jrhun/TeensyEngine/buildLog/designProfile.PNG

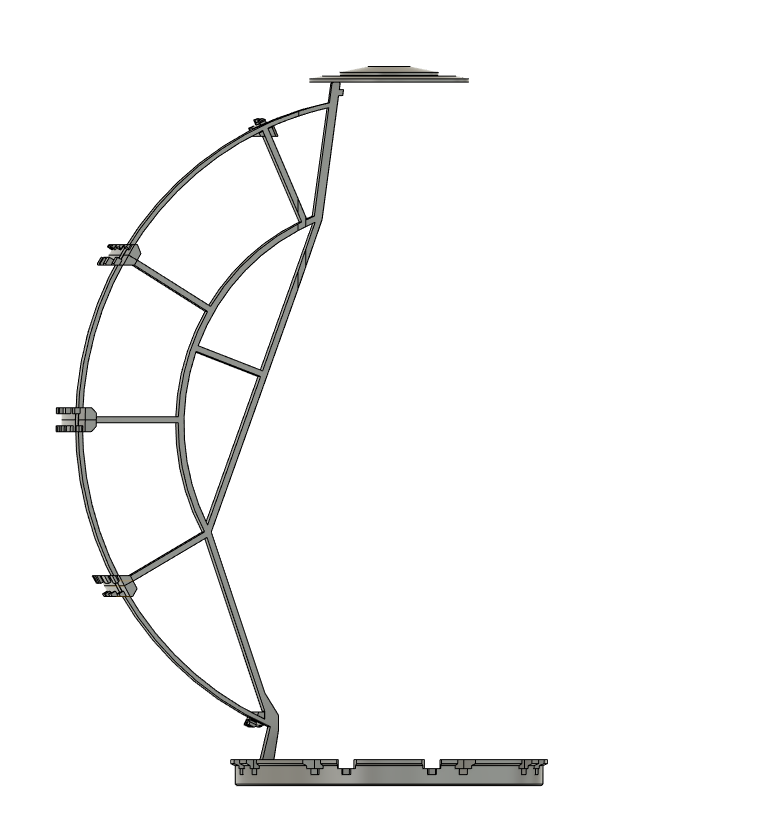
buildLog/designProfile.PNG
