jrhun/TeensyEngine/buildLog/PCB_design-front.PNG

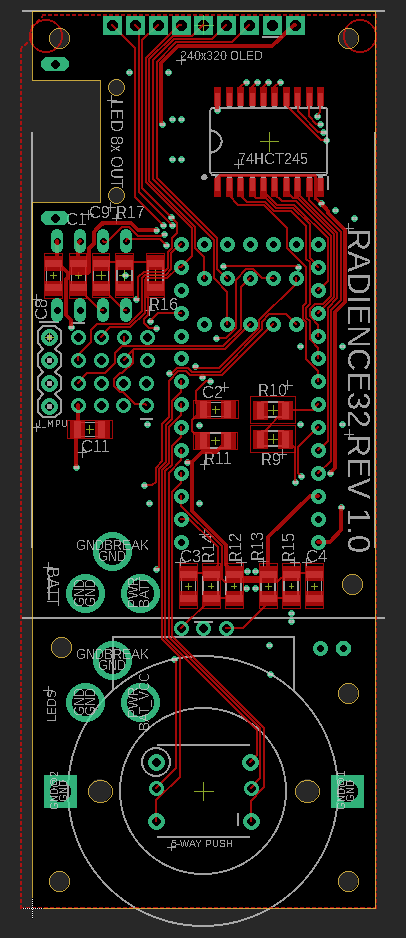
buildLog/PCB_design-front.PNG
