jrhun/TeensyEngine/images/flower/pixel_flowers_stages_of_blooming__16x16_px__by_brysiaa_de5okf2-fullview.jpg

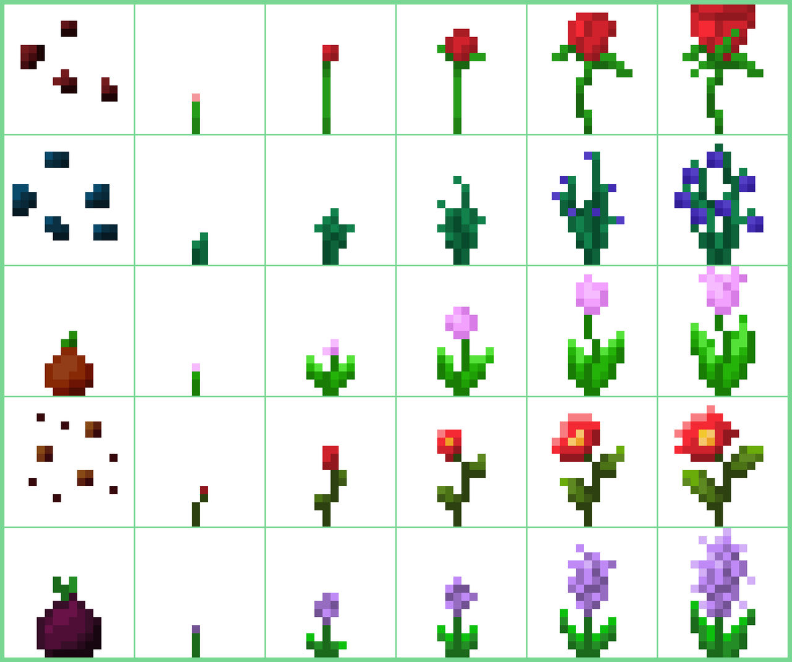
images/flower/pixel_flowers_stages_of_blooming__16x16_px__by_brysiaa_de5okf2-fullview.jpg
