jrhun/TeensyEngine/ledControl.h

//#ifndef LEDS_H
//#define LEDS_H
//
//#include "data.h"
//
////things to try stop flickering
////1
////#define FASTLED_ALLOW_INTERRUPTS
////2
//// change first pin to one earlier i.e 25 and skip first NUM_LEDS_PER_STRIP
//#include <FastLED.h>
////#include <FastLED_GFX.h>
////#include <Fonts/PicopixelFL.h>
//
//#define ROWS                32
//#define COLS                64
//#define NUM_LEDS            ROWS*COLS
//#define NUM_STRIPS          8
//#define NUM_LEDS_PER_STRIP  240  //we have 30 * 8 leds per strip
//#define LAST_VISIBLE_LED    1920  //(NUM_STRIPS * NUM_LEDS_PER_STRIP)
////#define FPS                 60
//
///*
//#if !defined(pgm_read_byte)
//#define pgm_read_byte(addr) (*(const unsigned char *)(addr))
//#endif
//#if !defined(pgm_read_word)
//#define pgm_read_word(addr) (*(const unsigned short *)(addr))
//#endif
//#if !defined(pgm_read_pointer)
//#define pgm_read_pointer(addr) ((void *)pgm_read_word(addr))
//#endif
//*/
//CRGBArray < NUM_LEDS > ledsRaw;
////uint8_t zBuffer[ROWS * COLS];
////CRGB scratchArray[NUM_LEDS]; // have global as ESP doesn't like variables on the stack
//CRGBPalette16 currentPalette;
//CRGBPalette16 targetPalette;
//TBlendType    currentBlending;
//uint8_t blendCounter = 0;
//bool blendActive = false;
//
//
////external variables
//
///*
//
//
//const uint8_t gGradientPaletteCount =
//  sizeof( gGradientPalettes) / sizeof( TProgmemRGBGradientPalettePtr );
//*/
//const uint8_t PROGMEM gamma8[] = {
//  0,   0,   0,   0,   0,   0,  0,  0,  0,  0,  0,  0,  0,  0,  0,  0,
//  0,   0,   0,   0,   0,   0,  0,  0,  0,  0,  0,  0,  1,  1,  1,  1,
//  1,   1,   1,   1,   1,   1,  1,  1,  1,  2,  2,  2,  2,  2,  2,  2,
//  2,   3,   3,   3,   3,   3,  3,  3,  4,  4,  4,  4,  4,  5,  5,  5,
//  5,   6,   6,   6,   6,   7,  7,  7,  7,  8,  8,  8,  9,  9,  9, 10,
//  10,  10,  11,  11,  11,  12, 12, 13, 13, 13, 14, 14, 15, 15, 16, 16,
//  17,  17,  18,  18,  19,  19, 20, 20, 21, 21, 22, 22, 23, 24, 24, 25,
//  25,  26,  27,  27,  28,  29, 29, 30, 31, 32, 32, 33, 34, 35, 35, 36,
//  37,  38,  39,  39,  40,  41, 42, 43, 44, 45, 46, 47, 48, 49, 50, 50,
//  51,  52,  54,  55,  56,  57, 58, 59, 60, 61, 62, 63, 64, 66, 67, 68,
//  69,  70,  72,  73,  74,  75, 77, 78, 79, 81, 82, 83, 85, 86, 87, 89,
//  90,  92,  93,  95,  96,  98, 99, 101, 102, 104, 105, 107, 109, 110, 112, 114,
//  115, 117, 119, 120, 122, 124, 126, 127, 129, 131, 133, 135, 137, 138, 140, 142,
//  144, 146, 148, 150, 152, 154, 156, 158, 160, 162, 164, 167, 169, 171, 173, 175,
//  177, 180, 182, 184, 186, 189, 191, 193, 196, 198, 200, 203, 205, 208, 210, 213,
//  215, 218, 220, 223, 225, 228, 231, 233, 236, 239, 241, 244, 247, 249, 252, 255
//};
//
//void adjustGamma(CRGB &colour) {
//  colour.r = gamma8[colour.r];
//  colour.g = gamma8[colour.g];
//  colour.b = gamma8[colour.b];
//
//  //method 2
//  //  colour.r = dim8_video(colour.r);
//  //  colour.g = dim8_video(colour.g);
//  //  colour.b = dim8_video(colour.b);
//}
//
//uint16_t XY(uint8_t x, uint8_t y) {
//  /*//leds are mapped serpentine with 2 offset with 30 leds in each row e.g.
//    0       60
//    1       61
//    2   59  62  119
//    3   ..  63  ..
//    ..  33  ..  93
//    29  32  89  92
//        31      91
//        30      90
//  */
//
//  if ( (x >= COLS) || (y >= ROWS) )
//    return LAST_VISIBLE_LED + 1;
//
//  uint16_t j;
//  uint16_t i = x * (ROWS - 2); // each column actually has 30 leds
//  if (x % 2 == 0) {// even row
//    if (y == 31  and x >= 16 and x < 48) {
//      return (LAST_VISIBLE_LED + (x * 2) + (y - 30));
//    }
//    if ((y == 30 or y == 31) and (x < 16 or x >= 48)) {
//      //      return LAST_VISIBLE_LED + 1;
//      return (LAST_VISIBLE_LED + (x * 2) + (y - 30));
//    }
//    if (x >= 16 and x < 48)
//      j = y - 1;
//    else j = y;
//  }
//  else {// if odd row flip the row
//    if (y == 0 or y == 1) {
//      //      return LAST_VISIBLE_LED + 1;
//      return (LAST_VISIBLE_LED + (x * 2) + y);
//    }
//    j = (ROWS - 1) - y; //
//
//  }
//  return (i + j);
//}
//
//
//class Leds {
//  public:
//    Leds() {};// : FastLED_GFX(COLS, ROWS) {}
//
//    void init() {
//      #if defined(ESP32)
//      FastLED.addLeds<WS2812B, 13, GRB>(ledsRaw, 0 * NUM_LEDS_PER_STRIP, NUM_LEDS_PER_STRIP).setCorrection( TypicalSMD5050 );
//      FastLED.addLeds<WS2812B, 12, GRB>(ledsRaw, 1 * NUM_LEDS_PER_STRIP, NUM_LEDS_PER_STRIP).setCorrection( TypicalSMD5050 );
//      FastLED.addLeds<WS2812B, 14, GRB>(ledsRaw, 2 * NUM_LEDS_PER_STRIP, NUM_LEDS_PER_STRIP).setCorrection( TypicalSMD5050 );
//      FastLED.addLeds<WS2812B, 27, GRB>(ledsRaw, 3 * NUM_LEDS_PER_STRIP, NUM_LEDS_PER_STRIP).setCorrection( TypicalSMD5050 );
//      FastLED.addLeds<WS2812B, 26, GRB>(ledsRaw, 4 * NUM_LEDS_PER_STRIP, NUM_LEDS_PER_STRIP).setCorrection( TypicalSMD5050 );
//      FastLED.addLeds<WS2812B, 25, GRB>(ledsRaw, 5 * NUM_LEDS_PER_STRIP, NUM_LEDS_PER_STRIP).setCorrection( TypicalSMD5050 );
//      FastLED.addLeds<WS2812B, 33, GRB>(ledsRaw, 6 * NUM_LEDS_PER_STRIP, NUM_LEDS_PER_STRIP).setCorrection( TypicalSMD5050 );
//      FastLED.addLeds<WS2812B, 32, GRB>(ledsRaw, 7 * NUM_LEDS_PER_STRIP, NUM_LEDS_PER_STRIP).setCorrection( TypicalSMD5050 );
//      // teensy 4.x
//      #elif defined(__IMXRT1052__) || defined(__IMXRT1062__) 
//      FastLED.addLeds<NUM_STRIPS, WS2812B, 19, GRB>(ledsRaw, NUM_LEDS_PER_STRIP).setCorrection( TypicalSMD5050 );
//      #endif 
//      
//      FastLED.setBrightness( *Data::brightness_t );
//	    
//
//      FastLED.setTemperature( DirectSunlight );
//      //      FastLED.setMaxPowerInVoltsAndMilliamps(5, 5000);
//
//      currentPalette = RainbowColors_p;
//      currentBlending = LINEARBLEND;
//
////      setFont(&Picopixel);
////      setTextSize(1);
////      setTextWrap(true);
//      FastLED.setDither( 0 );
//
//      #if 0
//      //test strips
//      uint8_t j = 0;
//      while(true){
////      setTextSize(2);
//      j += 5;
//      for (int i = 0; i < 8; i++) {
//        
////        ledsRaw(i*NUM_LEDS_PER_STRIP + 10, i*NUM_LEDS_PER_STRIP + 15).fill_solid(CHSV(i * 26, 255, 255));
//        ledsRaw(i*NUM_LEDS_PER_STRIP + 17, i*NUM_LEDS_PER_STRIP + 17 + i).fill_solid(CRGB::Red);
////        setTextColor(CHSV(j, 255, 255));
////        setCursor(1+ i * COLS / 8, 10);
////        print(i);
//      }
////      setTextSize(1);
//      FastLED.show();
//      delay(50);
//      }
//      delay(10000);
//      #endif
//    }
//
//    void show() {
//       FastLED.show();
//    }
//
//    void drawPixel(int16_t x, int16_t y, CRGB color) {
//      ledsRaw[XY(x, y)] = color;
//    }
//    void drawPixel(int16_t x, int16_t y, uint8_t hue) {
//      ledsRaw[XY(x, y)] = getColour(hue);
//    }
//
//    void drawPixel(int16_t x, int16_t y, CRGB color, uint8_t amount) {
//      if (ledsRaw[XY(x, y)])
//        ledsRaw[XY(x, y)] = blend(ledsRaw[XY(x, y)], color, amount);
//      else
//        ledsRaw[XY(x, y)] = color.nscale8(amount);
//    }
//
//    void setRow(uint8_t row, CRGB colour) {
//      for (uint8_t x = 0; x < COLS; x++) {
//        ledsRaw[XY(x, row)] = colour;
//      }
//    }
//
//    void setRowRainbow(uint8_t row, uint8_t hue) {
//      CRGB *rowReference[COLS];
//
//      for (uint8_t x = 0; x < COLS; x++) {
//        rowReference[x] = &ledsRaw[XY(x, row)];
//      }
//      fill_rainbow(rowReference[0], COLS, hue);
//    }
//
//    void setCol(uint8_t col, CRGB colour) {
//      for (uint8_t y = 0; y < ROWS; y++) {
//        ledsRaw[XY(col, y)] = colour;
//      }
//    }
//
//    void setColRainbow(uint8_t col, uint8_t hue) {
//      CRGB *colReference[ROWS];
//      for (uint8_t y = 0; y < ROWS; y++) {
//        colReference[y] = &ledsRaw[XY(col, y)];
//      }
//      fill_rainbow(colReference[0], ROWS, hue);
//    }
//
//    CRGB getColour(uint8_t offset = 0) {
//      CRGB colour = ColorFromPalette( currentPalette, Data::hue + offset);
//      if (Data::adjustGamma)
//        adjustGamma(colour);
//      return colour;
//    }
//
//    void drawBlend(uint8_t row, uint8_t col, CRGB colour, uint8_t blendAmount) {
//      if (ledsRaw[XY(row, col)]) // only blend if pixel is already lit
//        nblend(ledsRaw[XY(row, col)], colour, blendAmount);
//      else
//        drawPixel(row, col, colour);
//    }
//
//    void fade(uint8_t amount = Data::fadeAmount) {
//      ledsRaw.fadeToBlackBy(amount);
//    }
//
//    void clear() {
//      fillScreen(CRGB::Black);
//    }
//
//    void fillScreen(CRGB color) {
//      ledsRaw.fill_solid(color);
//    }
//
//    bool blendOnDrawPixel = false;
//
//    // GFX OVERRIDDEN CLASSES BELOW
////    void drawLine(int16_t x0, int16_t y0, int16_t x1, int16_t y1, CRGB color) {
////      int16_t steep = abs(y1 - y0) > abs(x1 - x0);
////      if (steep) {
////        adagfxswap(x0, y0);
////        adagfxswap(x1, y1);
////      }
////
////      if (x0 > x1) {
////        adagfxswap(x0, x1);
////        adagfxswap(y0, y1);
////      }
////
////      int16_t dx, dy;
////      dx = x1 - x0;
////      dy = abs(y1 - y0);
////
////      int16_t err = dx / 2;
////      int16_t ystep;
////
////      if (y0 < y1) {
////        ystep = 1;
////      } else {
////        ystep = -1;
////      }
////
////      for (; x0 <= x1; x0++) {
////        if (steep) {
////          drawPixel(y0 % COLS, x0, color);
////        } else {
////          drawPixel(x0 % COLS, y0, color);
////        }
////        err -= dy;
////        if (err < 0) {
////          y0 += ystep;
////          err += dx;
////        }
////      }
////    }
////
////    void drawRGBBitmap(int16_t x, int16_t y,
////                       const uint16_t bitmap[], int16_t w, int16_t h) {
////      for (int16_t j = 0; j < h; j++, y++) {
////        for (int16_t i = 0; i < w; i++ ) {
////          uint16_t color = pgm_read_word(&bitmap[j * w + i]);
////          drawPixel(x + i, y, CRGB( pgm_read_byte(&gamma5[ color >> 11       ]),
////                                    pgm_read_byte(&gamma6[(color >> 5) & 0x3F]),
////                                    pgm_read_byte(&gamma5[ color       & 0x1F])));
////        }
////      }
////    }
////
////    void drawRGBBitmap(int16_t x, int16_t y,
////                       const uint8_t bitmap[], int16_t w, int16_t h) {
////      uint16_t buffOffset = 0;
////      uint8_t r, g, b;
////      for (int16_t j = 0; j < h; j++, y++) {
////        for (int16_t i = 0; i < w; i++ ) {
////          r = pgm_read_word(&bitmap[buffOffset++]);
////          g = pgm_read_word(&bitmap[buffOffset++]);
////          b = pgm_read_word(&bitmap[buffOffset++]);
////          drawPixel(x + i, y, CRGB(r, g, b));
////        }
////      }
////    }
////
////    // draw gradient scale between two colours fg and bg
////    void drawGrayscaleBitmap(int16_t x, int16_t y,
////                             const uint8_t bitmap[], int16_t w, int16_t h, CRGB fg, CRGB bg) {
////      // col = x * cos( uint8_t((y - COLS/2)*6) );
////      //          uint16_t iOffset = ((x+i) * cos8( uint8_t(y-ROWS/2)*6 )) / 256;
////      // therefore, if x = 0, i = 10, y = 0iOffset =
////      // 10 * cos8(-96=160) / 256 = 6. a 4 unit reduction
////      // but then we also need to blend with the other 4 pixels... otherwise lastone takes preference
////      uint16_t buffidx = 0;
////      for (int16_t j = 0; j < h; j++) {
////        for (int16_t i = 0; i < w; i++ ) {
////          //          CRGB colour = blend(fg, bg, (uint8_t)pgm_read_byte(&bitmap[j * w + i]));
////          CRGB colour = blend(bg, fg, pgm_read_byte(bitmap + buffidx));
////          buffidx++;
////          drawPixel((x + i + COLS) % COLS, j + y, colour);
////        }
////      }
////    }
//
//};
//
//Leds ledControl;
//
//// PATTERNS
//
///*
//  // use a x y z array
//  // with a 4 sided cube (no top/bottom
//  // each side represents the 32x64 led matrix
//  // one side is 64/ 4 = 16 wide, and 32 tall
//  // coordinates would be
//  // if we have a 32*32*32 grid though that we generate once
//  // then move the cube through it and interpolate between values
//
//
//  split the matrix into 4 sections
//  16x32, 16x32, 16x32, 16x32
//  1st section FRONT
//  so we would take col = x 0 to 15, row = y = 0 to 31, z = 0
//
//  2nd section RIGHT
//  col = z = 0 to 15, row = y = 0 to 31, x = 15
//  3rd section BACK
//  col = x = 15 to 0, row = y = 0 to 31, z = 15
//  4th section LEFT
//  col = z = 15 to 0, row = y = 0 to 31, x = 0
//
//  then we also offset the whole thing by
//  xOffset = 0 to 16, then zOffset = 0 to 16, then xoffset 16 to 0, then zoffset 16 to 0
//
//
//*/
//
//
//
//
//
//
//#if defined (ESP32)
//// -- The core to run FastLED.show()
//#define FASTLED_SHOW_CORE 0
//
//// -- Task handles for use in the notifications
//static TaskHandle_t FastLEDshowTaskHandle = 0;
//static TaskHandle_t userTaskHandle = 0;
//
//void FastLEDshowESP32()
//{
//  if (userTaskHandle == 0) {
//    const TickType_t xMaxBlockTime = pdMS_TO_TICKS( 200 );
//    // -- Store the handle of the current task, so that the show task can
//    //    notify it when it's done
//    userTaskHandle = xTaskGetCurrentTaskHandle();
//
//    // -- Trigger the show task
//    xTaskNotifyGive(FastLEDshowTaskHandle);
//
//    // -- Wait to be notified that it's done
//    ulTaskNotifyTake(pdTRUE, xMaxBlockTime);
//    userTaskHandle = 0;
//  }
//}
//
//void FastLEDshowTask(void *pvParameters)
//{
//  const TickType_t xMaxBlockTime = pdMS_TO_TICKS( 500 );
//  // -- Run forever...
//  for (;;) {
//    // -- Wait for the trigger
//    ulTaskNotifyTake(pdTRUE, xMaxBlockTime);
//
//    // -- Do the show (synchronously)
//    FastLED.show();
//
//    // -- Notify the calling task
//    xTaskNotifyGive(userTaskHandle);
//  }
//}
//
//#endif //ESP32
//
//
//#endif //LEDS_H
