jrhun/TeensyEngine/motion.h

#include "MPU9250.h"
#include "data.h"

MPU9250 IMU(Wire2, 0x68);
int status;

//float aRes;
//float gRes;
float quat[4] = {1.0f, 0.0f, 0.0f, 0.0f};
float GyroMeasError = PI * (40.0f / 180.0f);   // gyroscope measurement error in rads/s (start at 40 deg/s)
float GyroMeasDrift = PI * (0.0f  / 180.0f);   // gyroscope measurement drift in rad/s/s (start at 0.0 deg/s/s)
// There is a tradeoff in the beta parameter between accuracy and response speed.
// In the original Madgwick study, beta of 0.041 (corresponding to GyroMeasError of 2.7 degrees/s) was found to give optimal accuracy.
// However, with this value, the LSM9SD0 response time is about 10 seconds to a stable initial quaternion.
// Subsequent changes also require a longish lag time to a stable output, not fast enough for a quadcopter or robot car!
// By increasing beta (GyroMeasError) by about a factor of fifteen, the response time constant is reduced to ~2 sec
// I haven't noticed any reduction in solution accuracy. This is essentially the I coefficient in a PID control sense; 
// the bigger the feedback coefficient, the faster the solution converges, usually at the expense of accuracy. 
// In any case, this is the free parameter in the Madgwick filtering and fusion scheme.
float beta = sqrt(3.0f / 4.0f) * GyroMeasError;   // compute beta
float zeta = sqrt(3.0f / 4.0f) * GyroMeasDrift; 

float deltat = 0.0f, sum = 0.0f;   
float pitch, roll;


void initMPU() {

  status = IMU.begin();
  if (status < 0) {
    Serial.println("IMU initialization unsuccessful");
    Serial.println("Check IMU wiring or try cycling power");
    Serial.print("Status: ");
    Serial.println(status);
  }

  // setting the accelerometer full scale range to +/-8G
  //  aRes = 8.0/32768.0;
  IMU.setAccelRange(MPU9250::ACCEL_RANGE_8G);
  // setting the gyroscope full scale range to +/-500 deg/s
  //  gRes = 500.0/32768.0;
  IMU.setGyroRange(MPU9250::GYRO_RANGE_500DPS);
  // setting DLPF bandwidth to 20 Hz
  IMU.setDlpfBandwidth(MPU9250::DLPF_BANDWIDTH_20HZ);
  // setting SRD to 19 for a 50 Hz update rate
  IMU.setSrd(19);

//  IMU.calibrateAccel();
//  if (status > 0)
//    Serial.println("Accel calibrated");

//  status = IMU.calibrateMag();
//  if (status > 0) {
//    Serial.println("Mag calibrated");
//  }
}


void updateMPU() {
  IMU.readSensor();
//  Data::ax = IMU.getAccelY_mss();
//  Data::ay = IMU.getAccelZ_mss();
//  Data::az = IMU.getAccelX_mss();
//  Data::gx = IMU.getGyroX_rads();
//  Data::gy = IMU.getGyroY_rads();
//  Data::gz = IMU.getGyroZ_rads();
}

void getPitchBasic(){
//  updateMPU();
  IMU.readSensor();
  
  const float alpha = 0.5;
  
  static double fXg = 0;
  static double fYg = 0;
  static double fZg = 0;
  //Low Pass Filter
    fXg = IMU.getAccelY_mss() * alpha + (fXg * (1.0 - alpha));
    fYg = IMU.getAccelZ_mss() * alpha + (fYg * (1.0 - alpha));
    fZg = IMU.getAccelX_mss() * alpha + (fZg * (1.0 - alpha));

    Data::ax = fXg; 
    Data::ay = fZg; 
    Data::az = fYg; //i dont understand why I had these different here and above, but it currently works and matches pitch/roll
 
    //Roll & Pitch Equations
    // initial pitch negative, roll positive
    // 1st try, pitch negative, roll negative
    Data::pitch  = -(atan2(-fYg, fZg)*180.0)/M_PI;
    Data::roll = -(atan2(fXg, sqrt(fYg*fYg + fZg*fZg))*180.0)/M_PI;

//  Serial.print("Pitch: ");
//  Serial.println(Data::pitch,5);
//  Serial.print("Roll: ");
//  Serial.println(Data::roll,5);
}


void MadgwickQuaternionUpdate(float ax, float ay, float az, float gx, float gy, float gz, float mx, float my, float mz)
{
  float q1 = quat[0], q2 = quat[1], q3 = quat[2], q4 = quat[3];   // short name local variable for readability
  float norm;
  float hx, hy, _2bx, _2bz;
  float s1, s2, s3, s4;
  float qDot1, qDot2, qDot3, qDot4;

  // Auxiliary variables to avoid repeated arithmetic
  float _2q1mx;
  float _2q1my;
  float _2q1mz;
  float _2q2mx;
  float _4bx;
  float _4bz;
  float _2q1 = 2.0f * q1;
  float _2q2 = 2.0f * q2;
  float _2q3 = 2.0f * q3;
  float _2q4 = 2.0f * q4;
  float _2q1q3 = 2.0f * q1 * q3;
  float _2q3q4 = 2.0f * q3 * q4;
  float q1q1 = q1 * q1;
  float q1q2 = q1 * q2;
  float q1q3 = q1 * q3;
  float q1q4 = q1 * q4;
  float q2q2 = q2 * q2;
  float q2q3 = q2 * q3;
  float q2q4 = q2 * q4;
  float q3q3 = q3 * q3;
  float q3q4 = q3 * q4;
  float q4q4 = q4 * q4;

  // Normalise accelerometer measurement
  norm = sqrtf(ax * ax + ay * ay + az * az);
  if (norm == 0.0f) return; // handle NaN
  norm = 1.0f / norm;
  ax *= norm;
  ay *= norm;
  az *= norm;

  // Normalise magnetometer measurement
  norm = sqrtf(mx * mx + my * my + mz * mz);
  if (norm == 0.0f) return; // handle NaN
  norm = 1.0f / norm;
  mx *= norm;
  my *= norm;
  mz *= norm;

  // Reference direction of Earth's magnetic field
  _2q1mx = 2.0f * q1 * mx;
  _2q1my = 2.0f * q1 * my;
  _2q1mz = 2.0f * q1 * mz;
  _2q2mx = 2.0f * q2 * mx;
  hx = mx * q1q1 - _2q1my * q4 + _2q1mz * q3 + mx * q2q2 + _2q2 * my * q3 + _2q2 * mz * q4 - mx * q3q3 - mx * q4q4;
  hy = _2q1mx * q4 + my * q1q1 - _2q1mz * q2 + _2q2mx * q3 - my * q2q2 + my * q3q3 + _2q3 * mz * q4 - my * q4q4;
  _2bx = sqrtf(hx * hx + hy * hy);
  _2bz = -_2q1mx * q3 + _2q1my * q2 + mz * q1q1 + _2q2mx * q4 - mz * q2q2 + _2q3 * my * q4 - mz * q3q3 + mz * q4q4;
  _4bx = 2.0f * _2bx;
  _4bz = 2.0f * _2bz;

  // Gradient decent algorithm corrective step
  s1 = -_2q3 * (2.0f * q2q4 - _2q1q3 - ax) + _2q2 * (2.0f * q1q2 + _2q3q4 - ay) - _2bz * q3 * (_2bx * (0.5f - q3q3 - q4q4) + _2bz * (q2q4 - q1q3) - mx) + (-_2bx * q4 + _2bz * q2) * (_2bx * (q2q3 - q1q4) + _2bz * (q1q2 + q3q4) - my) + _2bx * q3 * (_2bx * (q1q3 + q2q4) + _2bz * (0.5f - q2q2 - q3q3) - mz);
  s2 = _2q4 * (2.0f * q2q4 - _2q1q3 - ax) + _2q1 * (2.0f * q1q2 + _2q3q4 - ay) - 4.0f * q2 * (1.0f - 2.0f * q2q2 - 2.0f * q3q3 - az) + _2bz * q4 * (_2bx * (0.5f - q3q3 - q4q4) + _2bz * (q2q4 - q1q3) - mx) + (_2bx * q3 + _2bz * q1) * (_2bx * (q2q3 - q1q4) + _2bz * (q1q2 + q3q4) - my) + (_2bx * q4 - _4bz * q2) * (_2bx * (q1q3 + q2q4) + _2bz * (0.5f - q2q2 - q3q3) - mz);
  s3 = -_2q1 * (2.0f * q2q4 - _2q1q3 - ax) + _2q4 * (2.0f * q1q2 + _2q3q4 - ay) - 4.0f * q3 * (1.0f - 2.0f * q2q2 - 2.0f * q3q3 - az) + (-_4bx * q3 - _2bz * q1) * (_2bx * (0.5f - q3q3 - q4q4) + _2bz * (q2q4 - q1q3) - mx) + (_2bx * q2 + _2bz * q4) * (_2bx * (q2q3 - q1q4) + _2bz * (q1q2 + q3q4) - my) + (_2bx * q1 - _4bz * q3) * (_2bx * (q1q3 + q2q4) + _2bz * (0.5f - q2q2 - q3q3) - mz);
  s4 = _2q2 * (2.0f * q2q4 - _2q1q3 - ax) + _2q3 * (2.0f * q1q2 + _2q3q4 - ay) + (-_4bx * q4 + _2bz * q2) * (_2bx * (0.5f - q3q3 - q4q4) + _2bz * (q2q4 - q1q3) - mx) + (-_2bx * q1 + _2bz * q3) * (_2bx * (q2q3 - q1q4) + _2bz * (q1q2 + q3q4) - my) + _2bx * q2 * (_2bx * (q1q3 + q2q4) + _2bz * (0.5f - q2q2 - q3q3) - mz);
  norm = sqrtf(s1 * s1 + s2 * s2 + s3 * s3 + s4 * s4);    // normalise step magnitude
  norm = 1.0f / norm;
  s1 *= norm;
  s2 *= norm;
  s3 *= norm;
  s4 *= norm;

  // Compute rate of change of quaternion
  qDot1 = 0.5f * (-q2 * gx - q3 * gy - q4 * gz) - beta * s1;
  qDot2 = 0.5f * (q1 * gx + q3 * gz - q4 * gy) - beta * s2;
  qDot3 = 0.5f * (q1 * gy - q2 * gz + q4 * gx) - beta * s3;
  qDot4 = 0.5f * (q1 * gz + q2 * gy - q3 * gx) - beta * s4;

  // Integrate to yield quaternion
  q1 += qDot1 * deltat;
  q2 += qDot2 * deltat;
  q3 += qDot3 * deltat;
  q4 += qDot4 * deltat;
  norm = sqrtf(q1 * q1 + q2 * q2 + q3 * q3 + q4 * q4);    // normalise quaternion
  norm = 1.0f / norm;
  quat[0] = q1 * norm;
  quat[1] = q2 * norm;
  quat[2] = q3 * norm;
  quat[3] = q4 * norm;

}


void getPitch() {
  IMU.readSensor();
  MadgwickQuaternionUpdate(IMU.getAccelX_mss(), IMU.getAccelY_mss(), IMU.getAccelZ_mss(), IMU.getGyroX_rads(), IMU.getGyroY_rads(), IMU.getGyroZ_rads(),  IMU.getMagY_uT(),  IMU.getMagX_uT(), IMU.getMagZ_uT());
  pitch = -asin(2.0f * (quat[1] * quat[3] - quat[0] * quat[2]));
  pitch *= 180.0f / PI;
  roll  = atan2(2.0f * (quat[0] * quat[1] + quat[2] * quat[3]), quat[0] * quat[0] - quat[1] * quat[1] - quat[2] * quat[2] + quat[3] * quat[3]);
  roll *= 180.0f / PI;

  Serial.print("Pitch: ");
  Serial.println(pitch,5);
  Serial.print("Roll: ");
  Serial.println(roll,5);
}

void loopMPU() {
  IMU.readSensor();

  // display the data
  Serial.print(IMU.getAccelX_mss(), 6);
  Serial.print("\t");
  Serial.print(IMU.getAccelY_mss(), 6);
  Serial.print("\t");
  Serial.print(IMU.getAccelZ_mss(), 6);
  Serial.print("\t");
  Serial.print(IMU.getGyroX_rads(), 6);
  Serial.print("\t");
  Serial.print(IMU.getGyroY_rads(), 6);
  Serial.print("\t");
  Serial.print(IMU.getGyroZ_rads(), 6);
  Serial.print("\t");
  Serial.print(IMU.getMagX_uT(), 6);
  Serial.print("\t");
  Serial.print(IMU.getMagY_uT(), 6);
  Serial.print("\t");
  Serial.print(IMU.getMagZ_uT(), 6);
  Serial.print("\t");
  Serial.println(IMU.getTemperature_C(), 6);
}
