jrhun/TeensyEngine/src/Patterns/PatternPictures.h

#pragma once

#include "Pattern.h"

static const uint8_t PROGMEM world_64_32_8bit[2048] = {
	0x00, 0x00, 0x00, 0x00, 0x00, 0x00, 0x00, 0x00, 0x00, 0x00, 0x00, 0x00, 0x00, 0x00, 0x00, 0x00, 0x7f, 0xaa, 0xca, 0xb3, 0xaa, 0xaa, 0xbf, 0xcb, 0xcb, 0xb1, 0x4f, 0x00, 0x00, 0x00, 0x00, 0x00, 0x00, 0x00, 0x00, 0x00, 0x00, 0x00, 0x00, 0x00, 0x00, 0x00, 0x00, 0x00, 0x00, 0x00, 0x00, 0x00, 0x00, 0x00, 0x00, 0x00, 0x00, 0x00, 0x00, 0x00, 0x00, 0x00, 0x00, 0x00, 0x00, 0x00, 0x00, 0x00,
	0x00, 0x00, 0x00, 0x00, 0x00, 0x00, 0x00, 0x00, 0x00, 0x00, 0x4f, 0x8f, 0x90, 0x99, 0xb4, 0xb8, 0xd3, 0xa2, 0x8c, 0xd1, 0xff, 0xff, 0xff, 0xff, 0xff, 0x86, 0x00, 0x00, 0x00, 0x00, 0x00, 0x00, 0x00, 0x00, 0x00, 0x00, 0x00, 0x00, 0x00, 0x38, 0xb1, 0xd7, 0xcb, 0x70, 0x00, 0x00, 0x00, 0x00, 0x00, 0x00, 0x00, 0x00, 0x00, 0x00, 0x00, 0x00, 0x00, 0x00, 0x00, 0x00, 0x00, 0x00, 0x00, 0x00,
	0x00, 0x00, 0x00, 0x86, 0xb4, 0xbf, 0xaa, 0x7c, 0x9a, 0x91, 0xdd, 0xf6, 0xd9, 0xb8, 0xbc, 0xf2, 0xef, 0xb8, 0x00, 0x38, 0xfb, 0xff, 0xff, 0xff, 0xad, 0x00, 0x00, 0x00, 0x00, 0x00, 0x90, 0xc2, 0x91, 0x42, 0x00, 0x38, 0x80, 0xc0, 0xda, 0xfb, 0xff, 0xff, 0xff, 0xff, 0xff, 0xff, 0xdd, 0xd7, 0xe7, 0xd1, 0xc5, 0x90, 0x86, 0x90, 0x70, 0x00, 0x00, 0x00, 0x00, 0x00, 0x00, 0x00, 0x00, 0x00,
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
	0x0000, 0x8000, 0xdbe2, 0xdbe2, 0xdbe2, 0xdbe2, 0xdbe2, 0xdbe2, 0xdbe2, 0xdbe2, 0xdbe2, 0xdbe2, 0xdbe2, 0xdbe2, 0xdbe2, 0xdbe2, 0xdbe2, 0xdbe2, 0xdbe2, 0xdbe2, 0xdbe2, 0xdbe2, 0xdbe2, 0xdbe2, 0xdbe2, 0x8000, 0x0000
};

static const uint16_t PROGMEM mario_cloud_13_9_16bit[117] = {
	0x0000, 0x0000, 0x0000, 0x0000, 0x0000, 0x8000, 0x8000, 0x8000, 0x8000, 0x0000, 0x0000, 0x0000, 0x0000,
	0x0000, 0x0000, 0x0000, 0x0000, 0x8000, 0xffff, 0xffff, 0xffff, 0xffff, 0x8000, 0x0000, 0x0000, 0x0000,
	0x0000, 0x0000, 0x8000, 0x8000, 0xffff, 0xffff, 0xffff, 0xffff, 0xffff, 0xffff, 0x8000, 0x0000, 0x0000,
	0x0000, 0x8000, 0xffff, 0xffff, 0xffff, 0xffff, 0xffff, 0xffff, 0xffff, 0xffff, 0x8000, 0x0000, 0x0000,
	0x0000, 0x8000, 0xffff, 0x9eff, 0xffff, 0xffff, 0xffff, 0xffff, 0x9eff, 0xffff, 0xffff, 0x8000, 0x0000,
	0x8000, 0xffff, 0xffff, 0xffff, 0x9eff, 0x9eff, 0x9eff, 0x9eff, 0xffff, 0xffff, 0xffff, 0xffff, 0x8000,
	0x0000, 0x8000, 0xffff, 0xffff, 0xffff, 0xffff, 0xffff, 0xffff, 0xffff, 0xffff, 0xffff, 0xffff, 0x8000,
	0x0000, 0x0000, 0x8000, 0xffff, 0xffff, 0x8000, 0x8000, 0x8000, 0xffff, 0x8000, 0xffff, 0x8000, 0x0000,
	0x0000, 0x0000, 0x0000, 0x8000, 0x8000, 0x0000, 0x0000, 0x0000, 0x8000, 0x0000, 0x8000, 0x0000, 0x0000
};




#if !defined(pgm_read_byte)
#define pgm_read_byte(addr) (*(const unsigned char *)(addr))
#endif
#if !defined(pgm_read_word)
#define pgm_read_word(addr) (*(const unsigned short *)(addr))
#endif

#if !defined(pgm_read_qword)
#define pgm_read_qword(addr) (*(const unsigned long *)(addr))
#endif



// grayscale 8 bit image
void drawGrayscaleBitmap(int16_t x, int16_t y,
	const uint8_t bitmap[], int16_t w, int16_t h, CRGB fg, CRGB bg) {
	uint16_t buffidx = 0;
	for (int16_t j = 0; j < h; j++) {
		for (int16_t i = 0; i < w; i++) {
			//          CRGB colour = blend(fg, bg, (uint8_t)pgm_read_byte(&bitmap[j * w + i]));
			CRGB colour = blend(bg, fg, pgm_read_byte(bitmap + buffidx));
			buffidx++;
			gfx.putPixel((x + i + SCREEN_WIDTH) % SCREEN_WIDTH, j + y, colour);
		}
	}
}

void drawGrayscaleBitmapColour(int16_t x, int16_t y, const uint8_t bitmap[], int16_t w, int16_t h, uint8_t hue) {
	//colourise greyscale bitmap 0
	for (int16_t j = 0; j < h; j++) {
		for (int16_t i = 0; i < w; i++) {
			uint8_t color = pgm_read_byte(&bitmap[j * w + i]);
			if (color != 0x00) { //treat black as alpha 
				// if closer to white then turn down saturation 
				// clamp val at 128 minimum to keep from getting too dark 
				// 0 - 127
				uint8_t sat = 0;
				uint8_t val = 0;
				//if (color > 127) {
				//	// 128 - 255, val = 255, sat from 255 to 127
				//	val = 255; 
				//	sat = myMap(color, 128, 255, 255, 127);
				//}
				//else {
				//	sat = 255;
				//	val = color + 127;
				//}
				CRGB c = CHSV(hue, 255, color);
				gfx.putPixel((i + x) % SCREEN_WIDTH, j + y, c);
			}
		}
	}
}

// 16bit 565 encoded image
void drawRGBBitmap(int16_t x, int16_t y,
	const uint16_t bitmap[], int16_t w, int16_t h, float hueShift = 0.0) {
	if (hueShift != 0) {
		gfx.rotateCalculate(hueShift);
	}
	for (int16_t j = 0; j < h; j++) {
		for (int16_t i = 0; i < w; i++) {
			uint16_t color = pgm_read_word(&bitmap[j * w + i]);
			if (color != 0x0000) {
				//treat black as alpha
				if (hueShift == 0) {
					gfx.putPixel((x + i) % SCREEN_WIDTH, j + y, CRGB(pgm_read_byte(&gamma5[color >> 11]),
						pgm_read_byte(&gamma6[(color >> 5) & 0x3F]),
						pgm_read_byte(&gamma5[color & 0x1F])));
				}
				else {
					CRGB c = CRGB(pgm_read_byte(&gamma5[color >> 11]),
						pgm_read_byte(&gamma6[(color >> 5) & 0x3F]),
						pgm_read_byte(&gamma5[color & 0x1F]));
					gfx.putPixel((x + i) % SCREEN_WIDTH, j + y, gfx.rotate(c));
				}
			}
		}
	}
}

//16bit a555 encoded image
void drawARGBBitmap(int16_t x, int16_t y,
	const uint16_t bitmap[], int16_t w, int16_t h, bool flip = false) {

	for (int16_t j = 0; j < h; j++) {
		for (int16_t i = 0; i < w; i++) {
			uint16_t color = pgm_read_word(&bitmap[j * w + i]);
			if (((color >> 15) & 0x01) == 1) { //if alpha 
				uint8_t r = pgm_read_byte(&gamma5[(color >> 10) & 0x1F]);
				uint8_t g = pgm_read_byte(&gamma5[(color >> 5) & 0x1F]);
				uint8_t b = pgm_read_byte(&gamma5[(color >> 0) & 0x1F]);
				uint16_t xPos = (flip) ? SCREEN_WIDTH - i - 1 : i;
				gfx.putPixel((xPos + x) % SCREEN_WIDTH, j + y, CRGB(r, g, b));
			}
		}
	}
}



//24bit R8G8B8 encoded image
void drawRGBBitmap24bit(int16_t x, int16_t y,
	const uint8_t buf_u8[], int16_t w, int16_t h, float hueShift = 0.0) {
	uint8_t px_size = 3;
	if (hueShift != 0) {
		gfx.rotateCalculate(hueShift);
	}
	CRGB color;
	for (int16_t j = 0; j < h; j++) {
		for (int16_t i = 0; i < w; i++) {
			uint32_t px = w * j * px_size + i * px_size;
			color.r = buf_u8[px];
			color.g = buf_u8[px + 1];
			color.b = buf_u8[px + 2];
			if (hueShift != 0) {
				color = gfx.rotate(color);
			}
			gfx.putPixel((i + x) % SCREEN_WIDTH, j + y, color);
		}
	}


}

class PatternWorld : public _Pattern {
public:
	PatternWorld() : _Pattern("World") {}



	uint8_t drawFrame() {

		CRGB bg = CHSV(157, 255, 255);
		CRGB fg = CHSV(93, 255, 255);
		static uint16_t offset = SCREEN_WIDTH;
		static uint8_t offsetDelay = 0;
		//#if defined(ARDUINO)
		//		ledControl.drawGrayscaleBitmap(offset / 8, 0, world_64_32_8bit, 64, 32, fg, bg);
		//#else 
		//		
		uint16_t buffidx = 0;
		for (int16_t j = 0; j < SCREEN_HEIGHT; j++) {
			for (int16_t i = 0; i < SCREEN_WIDTH; i++) {
				CRGB colour = blend(bg, fg, (world_64_32_8bit[buffidx]));
				buffidx++;
				gfx.putPixel(((offset)+i + SCREEN_WIDTH) % SCREEN_WIDTH, j + 0, colour);
			}
		}
		//#endif
		offsetDelay = (offsetDelay + 1) % 6;
		if (offsetDelay == 0)
			offset--;
		if (offset < 0)
			offset = SCREEN_WIDTH;
		return returnVal;
	}


};

class PatternWorld2 : public _Pattern {
public:
	PatternWorld2() : _Pattern("World (no water)") {}



	uint8_t drawFrame() {

		CRGB bg = CHSV(0, 0, 0);
		CRGB fg = gfx.getColour();// CHSV(93, 255, 255);
		static uint16_t offset = SCREEN_WIDTH;
		static uint8_t offsetDelay = 0;
		//#if defined(ARDUINO)
		//		ledControl.drawGrayscaleBitmap(offset / 8, 0, world_64_32_8bit, 64, 32, fg, bg);
		//#else 
		//		
		uint16_t buffidx = 0;
		for (int16_t j = 0; j < SCREEN_HEIGHT; j++) {
			for (int16_t i = 0; i < SCREEN_WIDTH; i++) {
				fg = gfx.getColour(-i - j / 2);
				CRGB colour = blend(bg, fg, (world_64_32_8bit[buffidx]));
				buffidx++;
				gfx.putPixel(((offset)+i) % SCREEN_WIDTH, j + 0, colour);
			}
		}
		//#endif
		offsetDelay = (offsetDelay + 1) % 6;
		if (offsetDelay == 0)
			offset--;
		if (offset < 0)
			offset = SCREEN_WIDTH;

		return returnVal;
	}


};

class PatternMario : public _Pattern {
public:
	PatternMario() : _Pattern("Mario") {}

	uint8_t drawFrame() {
		_Pattern::drawFrame();

		frameCounter = (frameCounter + 1) % 12;
		if (frameCounter == 0) {
			marioPosX = (marioPosX + 1) % SCREEN_WIDTH;
		}
		//draw from back to front
		gfx.clear();
		gfx.fill(CRGB(90, 142, 245)); //mario background colour
		//ground
		for (uint8_t i = 0; i < 8; i++) {
			drawARGBBitmap(SCREEN_WIDTH + i * 8 - staticPos, groundPosY, mario_ground_8_8_16bit, 8, 8);
		}
		//bush
		drawARGBBitmap(SCREEN_WIDTH + 7 - staticPos, 14, mario_bush_27_10_16bit, 27, 10);

		//cloud
		drawARGBBitmap(cloudPosX, (frame < 2) ? 2 : 3, mario_cloud_13_9_16bit, 13, 9);



		//mario
		if (lastFrameUpdate + ((unsigned long)(frameUpdateDelay)) < GET_MILLIS()) {
			frame = (frame + 1) % 6; // 0 - 2
			lastFrameUpdate = GET_MILLIS();
			//if (frame % 3 == 0) {
			//marioPosX = (marioPosX + 1) % SCREEN_WIDTH;
			//}
			cloudPosX = (SCREEN_WIDTH + cloudPosX - 1) % SCREEN_WIDTH;
			if (frame % 2 == 0)
				staticPos = (staticPos + 1) % SCREEN_WIDTH;
		}
		if (jump) {
			jump--;
			// jump counts down from 128
			float v = 1.0 - float(jump) / float(jumpTime); // convert from 0 - 1
			float yPos = 0;

			if (v < 0.4) {
				yPos = myMap(v, 0.0, 0.4, 0, jumpHeight);
			}
			else if (v < 0.6) {
				yPos = jumpHeight;
			}
			else {
				yPos = myMap(v, 0.6, 1.0, jumpHeight, 0);
			}
			drawARGBBitmap(marioPosX, marioPosY - yPos, mario_jump_16_16_16bit, 16, 16);
		}
		else {
			if ((frame % 3) == 0) {
				drawARGBBitmap(marioPosX, marioPosY, mario1_16_16_16bit, 16, 16);
			}
			else if ((frame % 3) == 1) {
				drawARGBBitmap(marioPosX, marioPosY, mario2_16_16_16bit, 16, 16);
			}
			else if ((frame % 3) == 2) {
				drawARGBBitmap(marioPosX, marioPosY, mario3_16_16_16bit, 16, 16);

			}
		}

		return returnVal;
	}

	void trigger() {
		jump = jumpTime;
	}

	uint8_t frame = 0;
	uint8_t frameUpdateDelay = 100; //msec, 66msec = 15FPS
	uint8_t frameCounter = 0;
	uint8_t jump = 0;
	uint8_t jumpTime = 100;
	const uint8_t jumpHeight = 7;
	unsigned long lastFrameUpdate = 0;
	uint8_t marioPosX = 33; //positions are from the top down 
	uint8_t marioPosY = 9;
	uint8_t cloudPosX = 42;
	const uint8_t groundPosY = 24;
	uint8_t staticPos = 0;


};



static const uint16_t PROGMEM mushroom_12_11_16bit[132] = {
	0x0000, 0x0000, 0x0000, 0xf821, 0xf821, 0xf821, 0xf821, 0xffff, 0xf821, 0x0000, 0x0000, 0x0000,
	0x0000, 0x0000, 0xf821, 0xf821, 0xffff, 0xf821, 0xf821, 0xf821, 0xf821, 0xf821, 0x0000, 0x0000,
	0x0000, 0xf821, 0xf821, 0xf821, 0xf821, 0xf821, 0xf821, 0xf821, 0xffff, 0xf821, 0xf821, 0x0000,
	0xf821, 0xf821, 0xffff, 0xf821, 0xf821, 0xf821, 0xffff, 0xf821, 0xf821, 0xf821, 0xf821, 0xc042,
	0xf821, 0xf821, 0xf821, 0xf821, 0xf821, 0xf821, 0xf821, 0xf821, 0xf821, 0xf821, 0xffff, 0xc042,
	0xf821, 0xf821, 0xf821, 0xf821, 0xffff, 0xf821, 0xf821, 0xffff, 0xf821, 0xf821, 0xf821, 0xc042,
	0x0000, 0xc042, 0xc042, 0xc042, 0xc042, 0xc042, 0xc042, 0xc042, 0xc042, 0xc042, 0xc042, 0x0000,
	0x0000, 0x0000, 0x0000, 0x0000, 0xb5b6, 0xb5b6, 0xb5b6, 0xb5b6, 0x0000, 0x0000, 0x0000, 0x0000,
	0x0000, 0x0000, 0x0000, 0x0000, 0xe73c, 0xe73c, 0xe73c, 0xb5b6, 0x0000, 0x0000, 0x0000, 0x0000,
	0x0000, 0x0000, 0x0000, 0x0000, 0xe73c, 0xe73c, 0xe73c, 0xb5b6, 0x0000, 0x0000, 0x0000, 0x0000,
	0x0000, 0x0000, 0x0000, 0x0000, 0xe73c, 0xe73c, 0xe73c, 0xb5b6, 0x0000, 0x0000, 0x0000, 0x0000
};

static const uint16_t PROGMEM mushroomNodots_12_11_16bit[132] = {
	0x0000, 0x0000, 0x0000, 0xf821, 0xf821, 0xf821, 0xf821, 0xf821, 0xf821, 0x0000, 0x0000, 0x0000,
	0x0000, 0x0000, 0xf821, 0xf821, 0xf821, 0xf821, 0xf821, 0xf821, 0xf821, 0xf821, 0x0000, 0x0000,
	0x0000, 0xf821, 0xf821, 0xf821, 0xf821, 0xf821, 0xf821, 0xf821, 0xf821, 0xf821, 0xf821, 0x0000,
	0xf821, 0xf821, 0xf821, 0xf821, 0xf821, 0xf821, 0xf821, 0xf821, 0xf821, 0xf821, 0xf821, 0xc042,
	0xf821, 0xf821, 0xf821, 0xf821, 0xf821, 0xf821, 0xf821, 0xf821, 0xf821, 0xf821, 0xf821, 0xc042,
	0xf821, 0xf821, 0xf821, 0xf821, 0xf821, 0xf821, 0xf821, 0xf821, 0xf821, 0xf821, 0xf821, 0xc042,
	0x0000, 0xc042, 0xc042, 0xc042, 0xc042, 0xc042, 0xc042, 0xc042, 0xc042, 0xc042, 0xc042, 0x0000,
	0x0000, 0x0000, 0x0000, 0x0000, 0xb5b6, 0xb5b6, 0xb5b6, 0xb5b6, 0x0000, 0x0000, 0x0000, 0x0000,
	0x0000, 0x0000, 0x0000, 0x0000, 0xe73c, 0xe73c, 0xe73c, 0xb5b6, 0x0000, 0x0000, 0x0000, 0x0000,
	0x0000, 0x0000, 0x0000, 0x0000, 0xe73c, 0xe73c, 0xe73c, 0xb5b6, 0x0000, 0x0000, 0x0000, 0x0000,
	0x0000, 0x0000, 0x0000, 0x0000, 0xe73c, 0xe73c, 0xe73c, 0xb5b6, 0x0000, 0x0000, 0x0000, 0x0000
};

class PatternMushroom : public _Pattern {
public:
	PatternMushroom() : _Pattern("Mushrooms") {}

	uint8_t drawFrame() {
		_Pattern::drawFrame();
		gfx.clear();

		//angle = myMap(GuiVars1, 0, 2, 0, angleMax);
		if (beat.getType() != beat.OFF) {
			angle = myMap(*beat, 0, 2552, 0, angleMax/2);
		}
		else if (++angleCounter > 7) {
			angleCounter = 0;
			if (angle == 0) {
				angle = angleMax;
			}
			else {
				angle--;
			}
		}

		if (++posCounter > 25) {
			posCounter = 0;
			pos = (pos + 1) % SCREEN_WIDTH;
		}
		uint8_t ybase = 12;

		float yPos = 0;
		if (jump) {
			jump--;
			// jump counts down from jumptime (100)
			float v = 1.0 - float(jump) / float(jumpTime); // convert from 0 - 1

			if (v < 0.4) {
				yPos = myMap(v, 0.0, 0.4, 0, jumpHeight);
			}
			else if (v < 0.6) {
				yPos = jumpHeight;
			}
			else {
				yPos = myMap(v, 0.6, 1.0, jumpHeight, 0);
			}
		}
		drawMushroom(pos, ybase - yPos);
		drawMushroom((pos + 21) % SCREEN_WIDTH, ybase - yPos);
		drawMushroom((pos + 42) % SCREEN_WIDTH, ybase - yPos);
		return returnVal;
	}

	void drawMushroom(uint8_t x, uint8_t y) {
		drawRGBBitmap(x, y, mushroom_12_11_16bit, 12, 11); //mushroom_12_11_16bit
		//drawDots(x, y);
	}

	void drawDots(uint8_t xOffset, uint8_t yOffset) {
		//12 x 4 size, 6 rows
		// we want to top row to 'rotate' slower than the bottom rows, less dots on the top (like a sphere rotating)

		uint8_t angle0 = myMap(angle, 0, angleMax, 0, 48); // visible from 6 to 16, 2 in loop %24
		uint8_t angle1 = myMap((angle + 8) % angleMax, 0, angleMax, 0, 64); // visible from 4 to 18, 3 in loop %20
		uint8_t angle2 = myMap((angle + 8) % angleMax, 0, angleMax, 0, 80); // visible from 2 to 20, 4 in loop %18
		uint8_t angle3 = myMap((angle + 0) % angleMax, 0, angleMax, 0, 96); // visible from 0 to 24, 5 in loop %14
		uint8_t angle4 = myMap((angle + 4) % angleMax, 0, angleMax, 0, 96); //
		uint8_t angle5 = myMap((angle + 12) % angleMax, 0, angleMax, 0, 96); // 


		if (angle0 % 16 >= 3 and angle0 % 16 <= 8) {
			gfx.putPixel((xOffset + angle0 % 16) % SCREEN_WIDTH, yOffset + 0, CRGB::White);
		}
		//else if (angle0 >= (3 + 16) and angle0 <= (8 + 16)) {
		//	gfx.putPixel((xOffset + angle0 - 16), yOffset + 0, CRGB::White);
		//}
		//else if (angle0 >= (3 + 32) and angle0 <= (8 + 32)) {
		//	gfx.putPixel((xOffset + angle0 - 32), yOffset + 0, CRGB::White);
		//}

		if (angle1 % 12 >= 3 and angle1 % 12 <= 9) {
			gfx.putPixel((xOffset + angle1 % 12) % SCREEN_WIDTH, yOffset + 1, CRGB::White);
			//gfx.putPixel(xOffset + (angle1 + 8)% 10, yOffset + 1, CRGB::White);
		}

		//if (angle2 % 12 >= 1 and angle2 % 12 <= 10) {
			//gfx.putPixel(xOffset + angle2 % 12, yOffset + 2, CRGB::White);
			//gfx.putPixel(xOffset + (angle2 +8 )% 10, yOffset + 2, CRGB::White);
		//}


		gfx.putPixel((xOffset + angle3 % 12) % SCREEN_WIDTH, yOffset + 3, CRGB::White);
		gfx.putPixel((xOffset + (angle3 + 6) % 12) % SCREEN_WIDTH, yOffset + 3, CRGB::White);

		
		//gfx.putPixel(xOffset + angle4 % 12, yOffset + 4, CRGB::White);
		//gfx.putPixel(xOffset + (angle4 + 6) % 12 , yOffset + 4, CRGB::White);

		gfx.putPixel((xOffset + angle5 % 12) % SCREEN_WIDTH, yOffset + 5, CRGB::White);
		gfx.putPixel((xOffset + (angle5 + 6)% 12) % SCREEN_WIDTH, yOffset + 5, CRGB::White);

	}


	void trigger() {
		jump = jumpTime;
	}
	uint8_t pos = 0;
	uint8_t posCounter = 0;
	uint8_t jump = 0;
	uint8_t jumpTime = 100;
	const uint8_t jumpHeight = 7;

	uint8_t angle = 0;
	uint8_t angleMax = 255;
	uint8_t angleCounter = 0;


};


static const uint16_t PROGMEM eye_bg_12_9_16bit[108] = {
	//A1R8G8B8
	//looking at them as an image should be on the left are are labed as such (but these are right eyes on a person)
	0x5ca6, 0x5ca6, 0x5ca6, 0x5ca6, 0x5ca6, 0x5ca6, 0x5ca6, 0x5ca6, 0x5ca6, 0x5ca6, 0x5ca6, 0x5ca6,
	0x7fff, 0x7fff, 0xffff, 0xffff, 0xffff, 0xffff, 0xffff, 0xffff, 0xffff, 0x5ca6, 0x5ca6, 0x5ca6,
	0x7fff, 0x7fff, 0xffff, 0xffff, 0xffff, 0xffff, 0xffff, 0xffff, 0xffff, 0xffff, 0x5ca6, 0x5ca6,
	0x7fff, 0xffff, 0xffff, 0xffff, 0xffff, 0xffff, 0xffff, 0xffff, 0xffff, 0xffff, 0xffff, 0xffff,
	0x7fff, 0xffff, 0xffff, 0xffff, 0xffff, 0xffff, 0xffff, 0xffff, 0xffff, 0xffff, 0xffff, 0xffff,
	0x5ca6, 0xffff, 0xffff, 0xffff, 0xffff, 0xffff, 0xffff, 0xffff, 0xffff, 0xffff, 0xffff, 0x5ca6,
	0x5ca6, 0x5ca6, 0xffff, 0xffff, 0xffff, 0xffff, 0xffff, 0xffff, 0xffff, 0xffff, 0x5ca6, 0x5ca6,
	0x5ca6, 0x5ca6, 0x5ca6, 0xffff, 0xffff, 0xffff, 0xffff, 0xffff, 0xffff, 0x5ca6, 0x5ca6, 0x5ca6,
	0x5ca6, 0x5ca6, 0x5ca6, 0x5ca6, 0x5ca6, 0x5ca6, 0x5ca6, 0x5ca6, 0x5ca6, 0x5ca6, 0x5ca6, 0x5ca6
};
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
public:
	PatternEyes() : _Pattern("Eyes") {}

	uint8_t drawFrame() {
		_Pattern::drawFrame();
		//draw background, iris (taking into account movement), then outline (overwrite iris)
		// if part of iris is outside of outline need to delete it (...)
		gfx.clear();
		//gfx.fill(CRGB::White);

		if ((random8() == 0) and (random8(4) == 0) and blinkCounter == 0 and winkCounter == 0) {
			blinkCounter = blinkCounterMax;
		}
		if ((random8() == 0) and (random8(10) == 0) and blinkCounter == 0 and winkCounter == 0) {
			winkCounter = winkCounterMax;
		}

		//uint8_t x = random8(); 
		//x = ease8InOutCubic(x);
		//x = lerp8by8(x, myMap(irisPosX, -3, 3, 0, 255), 128);
		//x = myMap(x, 0, 255, 0, irisHorizontalMovementMax*2);
		if (random8(64) == 0) {
			uint8_t x = random8();
			x = ease8InOutCubic(x / 2); //0 - 127 clustered around 0
			x = 127 + (random8(1) == 0) ? x : -x; //0-255 clustered around 127
			irisPosX = myMap(x, 0, 255, -2, 2);
		}
		//irisPosX = myMap(GuiVars1, 0, 2, -irisHorizontalMovementMax, irisHorizontalMovementMax);
		//irisPosY = myMap(GuiVars2, 0, 2, -irisVerticalMovementMax, irisVerticalMovementMax);
		if (beat.getType() != beat.OFF) {
			irisPosX = myMap(*beat, 0, 255, -irisHorizontalMovementMax, irisHorizontalMovementMax);
		}
		//eyebrowsOffestLeft = myMap(GuiVars3, 0, 2, 0, -3);
		EyeState esLeft = EyeState::NORMAL;
		EyeState esRight = EyeState::NORMAL;

		if (blinkCounter) {
			blinkCounter--;
			float p = myMap(blinkCounter, 0, blinkCounterMax, 0, 1);
			if (p > 0.90) {
				esLeft = esRight = EyeState::NORMAL;
			}
			else if (p > 0.80) {
				esLeft = EyeState::BLINK1;
			}
			else if (p > 0.6) {
				esLeft = esRight = EyeState::BLINK1;
			}
			else if (p > 0.40) {
				esLeft = EyeState::BLINK2;
				esRight = EyeState::BLINK1;
			}
			else {
				esLeft = esRight = EyeState::BLINK2;
				eyebrowsOffestLeft++;
				eyebrowsOffestRight++;
			}
		}
		if (winkCounter) {
			winkCounter--;
			float p = myMap(winkCounter, 0, winkCounterMax, 0, 1);
			if (p > 0.80) {
				esRight = EyeState::NORMAL;
			}
			else if (p > 0.50) {
				esRight = EyeState::BLINK1;
			}
			else {
				esRight = EyeState::BLINK2;
				eyebrowsOffestRight++;
			}
		}



		MouthState ms = mouthBaseState;

		if (raiseEyebrowsCounter) {
			raiseEyebrowsCounter--;
			float p = myMap(raiseEyebrowsCounter, 0, raiseEyebrowsCounterMax, 0, 1);
			if (p > 0.85) {
				eyebrowsOffestLeft = eyebrowsOffestRight = -1;
				ms = MouthState::NEUTRAL;
			}
			else if (p > 0.70) {
				eyebrowsOffestLeft = eyebrowsOffestRight = -2;
				ms = MouthState::SURPRISE1;
			}
			else if (p > 0.30) {
				eyebrowsOffestLeft = eyebrowsOffestRight = -3;
				ms = MouthState::SURPRISE2;
			}
			else if (p > 0.15) {
				eyebrowsOffestLeft = eyebrowsOffestRight = -2;
				ms = MouthState::SURPRISE1;
			}
			else {
				eyebrowsOffestLeft = eyebrowsOffestRight = -1;
				ms = MouthState::NEUTRAL;
			}

		}



		//uint8_t ms = myMap(GuiVars1, 0, 2, 0, MouthState::SMILE4 + 1);

		if ((random8() == 0) and (random8(2) == 0) and mouthCounter == 0 and raiseEyebrowsCounter == 0) {
			//change to new mouth position 
			mouthTargetState = (MouthState)myMap(random8(), 0, 255, 0, MouthState::SMILE4);
			mouthCounter = mouthCounterMax;
		}
		if (mouthCounter) {
			mouthCounter--;
			float i = myMap(mouthCounter, 0, mouthCounterMax, 0, 1);
			if (i > 0.7) {
				//go to targetState
				ms = (MouthState)interpolate((uint8_t)mouthBaseState, (uint8_t)mouthTargetState, myMap(i, 1, 0.7, 0, 1));
			}
			else if (i > 0.3) {
				//hold
				ms = mouthTargetState;
			}
			else {
				//go to baseState
				ms = (MouthState)interpolate((uint8_t)mouthTargetState, (uint8_t)mouthBaseState, myMap(i, 0.3, 0, 0, 1));
			}
		}

		if ((random8() == 0) and (random8(4) == 0) and (mouthCounter == 0) and (raiseEyebrowsCounter == 0)) {
			if (mouthBaseState == MouthState::NEUTRAL) {
				mouthBaseState = MouthState::SMILE4;
			}
			else {
				mouthBaseState = MouthState::NEUTRAL;
			}
		}

		drawEyes(irisPosX, irisPosY, esLeft, esRight, eyebrowsOffestLeft, eyebrowsOffestRight);
		drawMouth((MouthState)ms);
		uint8_t leftHolder = leftEyeX;
		uint8_t rightHolder = rightEyeX;
		leftEyeX += SCREEN_WIDTH / 2;
		rightEyeX += SCREEN_WIDTH / 2;
		//draw second set of eyes so we have 1 set on front, 1 set on back
		drawEyes(irisPosX, irisPosY, esLeft, esRight, eyebrowsOffestLeft, eyebrowsOffestRight);
		drawMouth((MouthState)ms);
		leftEyeX = leftHolder;
		rightEyeX = rightHolder;

		eyebrowsOffestLeft = 0;
		eyebrowsOffestRight = 0;



		return returnVal;

	}

	void trigger() {
		raiseEyebrowsCounter = raiseEyebrowsCounterMax;
	}

	uint8_t leftEyeX = 3;
	uint8_t rightEyeX = 14;
	uint8_t eyeY = 9;
	uint8_t eyeIrisOffestLeftX = 4;
	uint8_t eyeIrisOffestRightX = 4;
	uint8_t eyeIrisOffestY = 1;

	uint8_t eyebrowOffsetX = 0;
	int8_t eyebrowOffsetY = -3;

	uint8_t mouthOffsetX = 3;
	uint8_t mouthOffsetY = 10;

	int8_t irisPosX = 0;
	uint8_t irisHorizontalMovementMax = 3;
	int8_t irisPosY = 0;
	uint8_t irisVerticalMovementMax = 1;
	int8_t eyebrowsOffestLeft = 0;
	int8_t eyebrowsOffestRight = 0;

	uint8_t blinkCounter = 0;
	uint8_t blinkCounterMax = 30;
	uint8_t winkCounter = 0;
	uint8_t winkCounterMax = 50;
	uint8_t raiseEyebrowsCounter = 0;
	uint8_t raiseEyebrowsCounterMax = 120;
	uint16_t mouthCounter = 0;
	uint16_t mouthCounterMax = 260;

	enum MouthState {
		TONGUE3, TONGUE2, TONGUE1,
		NEUTRAL,
		SMILE1, SMILE2, SMILE3, SMILE4,
		SURPRISE1, SURPRISE2
	};
	MouthState mouthBaseState = MouthState::NEUTRAL;
	MouthState mouthTargetState = MouthState::NEUTRAL;

	const uint16_t* eyes[3] = {
	eye_fg_12_9_16bit,
	eye_fg_blink1_12_9_16bit,
	eye_fg_blink2_12_9_16bit
	};

	enum EyeState {
		NORMAL,
		BLINK1,
		BLINK2,
	};




	//blink 
	// set timer for blink time (not needed just run frames
	// set frame to 1, then 2, then 0 and exit blink routine 

	void drawEyes(int8_t dirX, int8_t dirY, EyeState left, EyeState right, int8_t leftEyebrows = 0, int8_t rightEyebrow = 0) {
		//left eye

		if (left == EyeState::NORMAL) {

			drawARGBBitmap(leftEyeX, eyeY, eye_bg_12_9_16bit, 12, 9, false); //left eye
			drawARGBBitmap(leftEyeX + eyeIrisOffestLeftX + CLAMP(dirX, -3, 2), eyeY + eyeIrisOffestY + dirY, eye_iris_6_6_16bit, 6, 6);
			drawARGBBitmap(leftEyeX, eyeY, eye_fg_12_9_16bit, 12, 9, false); //left eye
		}
		else if (left == EyeState::BLINK1) {
			drawARGBBitmap(leftEyeX, eyeY, eye_bg_blink1_12_9_16bit, 12, 9, false); //left eye
			dirX = CLAMP(dirX, -2, 2);
			drawARGBBitmap(leftEyeX + eyeIrisOffestLeftX + dirX, eyeY + eyeIrisOffestY + dirY, eye_iris_6_6_16bit, 6, 6);
			drawARGBBitmap(leftEyeX, eyeY, eye_fg_blink1_12_9_16bit, 12, 9, false); //left eye
		}
		else if (left == EyeState::BLINK2) {
			//dont need bg or eyes as eye closed
			drawARGBBitmap(leftEyeX, eyeY, eye_fg_blink2_12_9_16bit, 12, 9, false); //left eye
		}

		//right eye
		if (right == EyeState::NORMAL) {
			drawARGBBitmap(rightEyeX + 14, eyeY, eye_bg_12_9_16bit, 12, 9, true); //flip horizontal
			drawARGBBitmap(rightEyeX + eyeIrisOffestRightX + CLAMP(dirX, -2, 3), eyeY + eyeIrisOffestY + dirY, eye_iris_6_6_16bit, 6, 6);
			drawARGBBitmap(rightEyeX + 14, eyeY, eye_fg_12_9_16bit, 12, 9, true);
		}
		else if (right == EyeState::BLINK1) {
			drawARGBBitmap(rightEyeX + 14, eyeY, eye_bg_blink1_12_9_16bit, 12, 9, true); //flip horizontal
			dirX = CLAMP(dirX, -2, 2);
			drawARGBBitmap(rightEyeX + eyeIrisOffestRightX + dirX, eyeY + eyeIrisOffestY + dirY, eye_iris_6_6_16bit, 6, 6);
			drawARGBBitmap(rightEyeX + 14, eyeY, eye_fg_blink1_12_9_16bit, 12, 9, true);
		}
		else if (right == EyeState::BLINK2) {
			//dont need bg or eyes as eye closed
			drawARGBBitmap(rightEyeX + 14, eyeY, eye_fg_blink2_12_9_16bit, 12, 9, true);
		}

		//eyebrows
		drawARGBBitmap(leftEyeX + eyebrowOffsetX, eyeY + eyebrowOffsetY + leftEyebrows, eyebrow_12_3_16bit, 12, 3, false);
		drawARGBBitmap(rightEyeX + 14 + eyebrowOffsetX, eyeY + eyebrowOffsetY + rightEyebrow, eyebrow_12_3_16bit, 12, 3, true);
	}



	void drawMouth(MouthState m) {
		//colour 192, 204, 222, tongue (210, 84, 96), tongue inner (230, 130, 140)
		CRGB mouthColour = CRGB(192, 204, 222);//CRGB(192, 204, 222);
		CRGB mouthInnerColour = CRGB(230, 230, 230);
		CRGB tongueColour = CRGB(210, 84, 96);
		CRGB tongueColourInner = CRGB(230, 130, 140);

		uint8_t posX = mouthOffsetX + leftEyeX;
		uint8_t posY = mouthOffsetY + eyeY;


		if (m == MouthState::NEUTRAL) {
			gfx.drawLine(posX + 6, posY + 2, posX + 6, posY + 2, mouthColour);
			gfx.drawLine(posX + 7, posY + 3, posX + 11, posY + 3, mouthColour);
			gfx.drawLine(posX + 12, posY + 2, posX + 12, posY + 2, mouthColour);
		}
		else if (m == MouthState::SMILE1) {
			gfx.drawLine(posX + 5, posY + 2, posX + 6, posY + 2, mouthColour);
			gfx.drawLine(posX + 7, posY + 3, posX + 11, posY + 3, mouthColour);
			gfx.drawLine(posX + 12, posY + 2, posX + 13, posY + 2, mouthColour);
			gfx.putPixel(posX + 14, posY + 1, mouthColour);
		}
		else if (m == MouthState::SMILE2) {
			gfx.drawLine(posX + 4, posY + 1, posX + 4, posY + 1, mouthColour);
			gfx.drawLine(posX + 5, posY + 2, posX + 13, posY + 2, mouthColour);
			gfx.drawLine(posX + 7, posY + 3, posX + 11, posY + 3, mouthColour);
			gfx.drawLine(posX + 14, posY + 1, posX + 14, posY + 1, mouthColour);
		}
		else if (m == MouthState::SMILE3) {
			gfx.drawLine(posX + 3, posY + 1, posX + 3, posY + 1, mouthColour);
			gfx.drawLine(posX + 15, posY + 1, posX + 15, posY + 1, mouthColour);
			gfx.drawLine(posX + 4, posY + 2, posX + 14, posY + 2, mouthColour);
			gfx.drawLine(posX + 6, posY + 3, posX + 12, posY + 3, mouthColour);
			gfx.drawLine(posX + 7, posY + 3, posX + 11, posY + 3, mouthInnerColour);
			gfx.drawLine(posX + 7, posY + 4, posX + 11, posY + 4, mouthColour);

		}

		else if (m == MouthState::SMILE4) {
			//make more narrow
			gfx.putPixel(posX + 2, posY, mouthColour);
			gfx.putPixel(posX + 16, posY, mouthColour);
			gfx.drawLine(posX + 3, posY + 1, posX + 15, posY + 1, mouthColour);

			gfx.drawLine(posX + 5, posY + 2, posX + 13, posY + 2, mouthColour);
			gfx.drawLine(posX + 6, posY + 2, posX + 12, posY + 2, mouthInnerColour);

			gfx.drawLine(posX + 6, posY + 3, posX + 12, posY + 3, mouthColour);
			gfx.drawLine(posX + 7, posY + 3, posX + 11, posY + 3, mouthInnerColour);

			gfx.drawLine(posX + 7, posY + 4, posX + 11, posY + 4, mouthColour);
			//gfx.putPixel(posX, posY, mouthColour); 
			//gfx.putPixel(posX + 18, posY, mouthColour); 
			//gfx.drawLine(posX + 1, posY + 1, posX + 17, posY + 1, mouthColour);

			//gfx.drawLine(posX + 3, posY + 2, posX + 15, posY + 2, mouthColour);
			//gfx.drawLine(posX + 4, posY + 2, posX + 14, posY + 2, mouthInnerColour);

			//gfx.drawLine(posX + 4, posY + 3, posX + 14, posY + 3, mouthColour);
			//gfx.drawLine(posX + 5, posY + 3, posX + 13, posY + 3, mouthInnerColour);

			//gfx.drawLine(posX + 5, posY + 4, posX + 13, posY + 4, mouthColour);
		}
		else if (m == MouthState::TONGUE1) {
			gfx.drawLine(posX + 5, posY + 2, posX + 5, posY + 2, mouthColour);
			gfx.drawLine(posX + 6, posY + 3, posX + 12, posY + 3, mouthColour);
			gfx.drawLine(posX + 13, posY + 2, posX + 13, posY + 2, mouthColour);
			gfx.drawLine(posX + 8, posY + 4, posX + 12, posY + 4, tongueColour);
			gfx.drawLine(posX + 9, posY + 5, posX + 11, posY + 5, tongueColour);
			gfx.putPixel(posX + 10, posY + 4, tongueColourInner);

		}
		else if (m == MouthState::TONGUE2) {
			gfx.drawLine(posX + 4, posY + 2, posX + 5, posY + 2, mouthColour);
			gfx.drawLine(posX + 6, posY + 3, posX + 12, posY + 3, mouthColour);
			gfx.drawLine(posX + 13, posY + 2, posX + 14, posY + 2, mouthColour);
			gfx.drawLine(posX + 8, posY + 4, posX + 12, posY + 4, tongueColour);
			gfx.drawLine(posX + 8, posY + 5, posX + 12, posY + 5, tongueColour);
			gfx.drawLine(posX + 9, posY + 6, posX + 11, posY + 6, tongueColour);
			gfx.drawLine(posX + 10, posY + 4, posX + 10, posY + 5, tongueColourInner);
		}
		else if (m == MouthState::TONGUE3) {
			gfx.drawLine(posX + 3, posY + 1, posX + 3, posY + 1, mouthColour);
			gfx.drawLine(posX + 4, posY + 2, posX + 5, posY + 2, mouthColour);
			gfx.drawLine(posX + 6, posY + 3, posX + 12, posY + 3, mouthColour);
			gfx.drawLine(posX + 13, posY + 2, posX + 14, posY + 2, mouthColour);
			gfx.drawLine(posX + 15, posY + 1, posX + 15, posY + 1, mouthColour);
			gfx.drawLine(posX + 8, posY + 4, posX + 12, posY + 4, tongueColour);
			gfx.drawLine(posX + 8, posY + 5, posX + 12, posY + 5, tongueColour);
			gfx.drawLine(posX + 8, posY + 6, posX + 12, posY + 6, tongueColour);
			gfx.drawLine(posX + 9, posY + 7, posX + 11, posY + 7, tongueColour);
			gfx.drawLine(posX + 10, posY + 4, posX + 10, posY + 6, tongueColourInner);
		}
		else if (m == MouthState::SURPRISE1) {
			gfx.drawLine(posX + 5, posY + 2, posX + 6, posY + 2, mouthColour);
			gfx.drawLine(posX + 7, posY + 3, posX + 10, posY + 3, mouthColour);
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
		//count up from 0 to 2
		if (i < 1.0) {
			//0 - 1
			currentFrame = interpolate(0, (int)maxFrames, i);
		}
		else {
			//1-2
			currentFrame = interpolate((int)maxFrames, 0, i - 1);
		}
		currentFrame = CLAMP(currentFrame, 0, maxFrames - 1);

		//change to only had subset of hues, avoid green and washed out colours
		const uint8_t randomAmount = 10;
		uint8_t hue = FxFade;
		if (currentFlowerType == FlowerType::ROSES) {
			drawFlower((0 + flowerRotatePos) % SCREEN_WIDTH, 0, currentFrame, hues[currentHue] + random8(randomAmount));
			drawFlower((13 * 1 + flowerRotatePos) % SCREEN_WIDTH, 1, currentFrame, hues[(currentHue + 1) % maxHues] + random8(randomAmount));
			drawFlower((13 * 2 + flowerRotatePos) % SCREEN_WIDTH, 0, currentFrame, hues[(currentHue + 2) % maxHues] + random8(randomAmount));
			drawFlower((13 * 3 + flowerRotatePos) % SCREEN_WIDTH, 1, currentFrame, hues[(currentHue + 3) % maxHues] + random8(randomAmount));
			drawFlower((13 * 4 + flowerRotatePos) % SCREEN_WIDTH, 0, currentFrame, hues[(currentHue + 4) % maxHues] + random8(randomAmount));
		}
		else if (currentFlowerType == FlowerType::TULIPS) {
			drawTulip((0 + flowerRotatePos) % SCREEN_WIDTH, 0, currentFrame, huesTulip[(currentHue + 0) % maxHues] + random8(randomAmount));
			drawTulip((13 * 1 + flowerRotatePos) % SCREEN_WIDTH, 1, currentFrame, huesTulip[(currentHue + 1) % maxHues] + random8(randomAmount));
			drawTulip((13 * 2 + flowerRotatePos) % SCREEN_WIDTH, 0, currentFrame, huesTulip[(currentHue + 2) % maxHues] + random8(randomAmount));
			drawTulip((13 * 3 + flowerRotatePos) % SCREEN_WIDTH, 1, currentFrame, huesTulip[(currentHue + 3) % maxHues] + random8(randomAmount));
			drawTulip((13 * 4 + flowerRotatePos) % SCREEN_WIDTH, 0, currentFrame, huesTulip[(currentHue + 4) % maxHues] + random8(randomAmount));
		}



		//change hue at end of frame counter
		frameCounter = (frameCounter + 1) % frameCounterMax;
		if (frameCounter == 0) {
			currentHue = (currentHue + 3) % maxHues;
			if (targetFlowerType != currentFlowerType) {
				currentFlowerType = targetFlowerType;
			}
		}
		//flowerRotateFrames++;
		if (flowerRotateFrames > 30) {
			flowerRotateFrames = 0;
			flowerRotatePos = (flowerRotatePos + 1) % SCREEN_WIDTH;
		}

		return returnVal;
	}

	void drawFlower(uint8_t x, uint8_t y, uint8_t frame, float hue) {
		if (frame == 0) {
			gfx.drawLine(flowerBaseOffsetX + x + 4, flowerBaseOffsetY + y + 8, flowerBaseOffsetX + x + 4, flowerBaseOffsetY + y + 9, CRGB(7, 21, 2));
			gfx.putPixel(flowerBaseOffsetX + x + 4, flowerBaseOffsetY + y + 7, CRGB(11, 34, 3));
		}
		else {
			drawRGBBitmap(flowerBaseOffsetX + x, flowerBaseOffsetY + y, flowerBase[frame], 10, 10);
		}


		//drawGrayscaleBitmapColour(flowerTopOffsetX + x, flowerTopOffsetY + y, flowerTop[frame], 8, 11, hue);

		//darkest to lightest 
		CRGB flower0 = CRGB(152, 25, 36); // CHSV(hue, 213, 153); //actual 
		CRGB flower1 = CRGB(206, 36, 47);
		CRGB flower2 = CRGB(242, 43, 48);
		CRGB flower3 = CRGB(251, 125, 131);

		//flower0.rotateCalculate(120);
		//float h = myMap(GuiVars1, 0, 2, 0, 360); //22.5, 45, 180, 225, 270, 306
		gfx.rotateCalculate(hue);
		flower0 = gfx.rotate(flower0);
		flower1 = gfx.rotate(flower1);
		flower2 = gfx.rotate(flower2);
		flower3 = gfx.rotate(flower3);

		//draw centre bit of flower (240, 61, 41) always as yellow
		CRGB flowerCentre0 = CRGB(240, 161, 41);
		CRGB flowerCentre1 = CRGB(245, 198, 107);
		CRGB flowerCentre2 = CRGB(244, 224, 162);
		if (frame == 1) {
			gfx.putPixel(flowerTopOffsetX + x + 6, flowerTopOffsetY + y + 10, flower0);
		}
		else if (frame == 2) {
			gfx.putPixel(flowerTopOffsetX + x + 5, flowerTopOffsetY + y + 5, flower1);
			gfx.putPixel(flowerTopOffsetX + x + 6, flowerTopOffsetY + y + 5, flower1);
			gfx.putPixel(flowerTopOffsetX + x + 5, flowerTopOffsetY + y + 6, flower1);
			gfx.putPixel(flowerTopOffsetX + x + 6, flowerTopOffsetY + y + 6, flower0);
			gfx.putPixel(flowerTopOffsetX + x + 5, flowerTopOffsetY + y + 7, flower0);
			gfx.putPixel(flowerTopOffsetX + x + 6, flowerTopOffsetY + y + 7, flower0);
		}
		if (frame == 3) {
			gfx.putPixel(flowerTopOffsetX + x + 5, flowerTopOffsetY + y + 5, flower0);
			gfx.putPixel(flowerTopOffsetX + x + 4, flowerTopOffsetY + y + 6, flower0);
			gfx.drawLine(flowerTopOffsetX + x + 3, flowerTopOffsetY + y + 5, flowerTopOffsetX + x + 4, flowerTopOffsetY + y + 5, flower1);
			gfx.putPixel(flowerTopOffsetX + x + 5, flowerTopOffsetY + y + 4, flower1);
			gfx.drawLine(flowerTopOffsetX + x + 4, flowerTopOffsetY + y + 3, flowerTopOffsetX + x + 5, flowerTopOffsetY + y + 3, flower2);
			gfx.putPixel(flowerTopOffsetX + x + 3, flowerTopOffsetY + y + 4, flower2);
			gfx.putPixel(flowerTopOffsetX + x + 3, flowerTopOffsetY + y + 3, flower3);
			gfx.putPixel(flowerTopOffsetX + x + 4, flowerTopOffsetY + y + 4, flowerCentre0);
		}
		else if (frame == 4) {
			//drawRGBBitmap(flowerTopOffsetX + x, flowerTopOffsetY + y, flower_top4_8_7_8bit, 8, 7, h);
			drawRGBBitmap24bit(flowerTopOffsetX + x, flowerTopOffsetY + y, flower_top4_8_7_24bit, 8, 7, hue);
			gfx.putPixel(flowerTopOffsetX + x + 4, flowerTopOffsetY + y + 4, flowerCentre0);
			gfx.putPixel(flowerTopOffsetX + x + 3, flowerTopOffsetY + y + 4, flowerCentre1);
			gfx.putPixel(flowerTopOffsetX + x + 4, flowerTopOffsetY + y + 3, flowerCentre1);
		}
		else if (frame == 5) {
			drawRGBBitmap24bit(flowerTopOffsetX + x, flowerTopOffsetY + y, flower_top5_8_7_24bit, 8, 7, hue);
			gfx.putPixel(flowerTopOffsetX + x + 4, flowerTopOffsetY + y + 4, flowerCentre0);
			gfx.putPixel(flowerTopOffsetX + x + 3, flowerTopOffsetY + y + 4, flowerCentre1);
			gfx.putPixel(flowerTopOffsetX + x + 4, flowerTopOffsetY + y + 3, flowerCentre1);
			gfx.putPixel(flowerTopOffsetX + x + 3, flowerTopOffsetY + y + 3, flowerCentre2);
		}
	}

	void drawTulip(uint8_t x, uint8_t y, uint8_t frame, float hue) {
		uint8_t baseX = x + tulipBaseOffsetX;
		uint8_t baseY = y + tulipBaseOffsetY;
		uint8_t topX = x + tulipTopOffsetX;
		uint8_t topY = y + tulipTopOffsetY;
		//hue = myMap(GuiVars1, 0, 2, 0, 360);
		gfx.rotateCalculate(hue);
		if (frame == 0) {
			//base
			gfx.putPixel(baseX + 4, baseY + 7, CRGB(30, 157, 6));
			gfx.putPixel(baseX + 4, baseY + 8, CRGB(25, 124, 5));
			gfx.putPixel(baseX + 4, baseY + 9, CRGB(25, 124, 5));
		}
		else if (frame == 1) {
			//base
			gfx.putPixel(baseX + 4, baseY + 9, CRGB(25, 124, 5));
			gfx.putPixel(baseX + 4, baseY + 8, CRGB(30, 157, 6));
			gfx.putPixel(baseX + 4, baseY + 7, CRGB(36, 179, 9));
			//gfx.putPixel(baseX + 3, baseY + 7, CRGB(30, 159,5));
			gfx.putPixel(baseX + 3, baseY + 8, CRGB(25, 124, 5));
			gfx.putPixel(baseX + 5, baseY + 7, CRGB(104, 218, 79));
			//gfx.putPixel(baseX + 5, baseY + 8, CRGB(25, 124, 5));

			//flower
			gfx.putPixel(baseX + 4, baseY + 6, gfx.rotate(CRGB(237, 117, 255)));
		}
		else if (frame == 2) {
			//extra offset as saving space (cutting top part of base out)
			const uint8_t additOffsetY = 5;
			drawRGBBitmap24bit(baseX, baseY + additOffsetY, tulip_base2_8_5_24bit, 8, 5);
			gfx.putPixel(baseX + 4, baseY + 4, gfx.rotate(CRGB(216, 56, 237)));
			gfx.putPixel(baseX + 4, baseY + 3, gfx.rotate(CRGB(237, 117, 255)));
			gfx.putPixel(baseX + 3, baseY + 4, gfx.rotate(CRGB(237, 117, 255)));

		}
		else if (frame == 3) {
			const uint8_t additOffsetX = 1;
			const uint8_t additOffsetY = 5;
			drawRGBBitmap24bit(baseX, baseY, tulip_base3_8_10_24bit, 8, 10);
			drawRGBBitmap24bit(topX + additOffsetX, topY + additOffsetY, tulip_top3_4_4_24bit, 4, 4, hue);
		}
		else if (frame == 4) {
			drawRGBBitmap24bit(baseX, baseY, tulip_base4_8_10_24bit, 8, 10);
			drawRGBBitmap24bit(topX, topY, tulip_top4_6_6_24bit, 6, 6, hue);
		}
		else if (frame == 5) {
			drawRGBBitmap24bit(baseX, baseY, tulip_base5_8_10_24bit, 8, 10);
			drawRGBBitmap24bit(topX, topY, tulip_top5_6_6_24bit, 6, 6, hue);
		}
	}

	void trigger() {
		if (currentFlowerType == FlowerType::ROSES)
			targetFlowerType = FlowerType::TULIPS;
		else
			targetFlowerType = FlowerType::ROSES;
	}

	uint8_t currentFrame = 0;
	const uint8_t maxFrames = 6;
	uint16_t frameCounter = 0;
	uint16_t frameCounterMax = 270;

	uint8_t flowerRotatePos = 0;
	uint8_t flowerRotateFrames = 0;

	uint8_t flowerBaseOffsetX = 1;
	uint8_t flowerBaseOffsetY = 14;
	uint8_t flowerTopOffsetX = 0;
	uint8_t flowerTopOffsetY = 9;

	uint8_t tulipBaseOffsetX = 1;
	uint8_t tulipBaseOffsetY = 14;
	uint8_t tulipTopOffsetX = 2;
	uint8_t tulipTopOffsetY = 8;

	enum FlowerType {
		ROSES,
		TULIPS
	} currentFlowerType, targetFlowerType;


	static const uint8_t maxHues = 7;
	const float hues[maxHues] = {
		//0, 27, 41, 138, 156, 191, 213
		0.0, 22.5, 45, 180, 225, 270, 306
	};
	const float huesTulip[maxHues] = {
		0.0, 36, 77, 118, 250, 290, 360
	};
	uint8_t currentHue = 0;


	const uint16_t* flowerBase[6] = {
		//R5G6B5
		flower_base1_10_10_16bit,
		flower_base1_10_10_16bit,
		flower_base2_10_10_16bit,
		flower_base3_10_10_16bit,
		flower_base4_10_10_16bit,
		flower_base5_10_10_16bit
	};
};
