jrhun/TeensyEngine/src/Palettes.h

#pragma once

#include "../data.h"
#include "Color.h"




//ideas for further
// Blackheartedwolf has some great ones
//http://soliton.vm.bytemark.co.uk/pub/cpt-city/bhw/index.html


// Gradient Color Palette definitions for 33 different cpt-city color palettes.
//    956 bytes of PROGMEM for all of the palettes together,
//   +618 bytes of PROGMEM for gradient palette code (AVR).
//  1,494 bytes total for all 34 color palettes and associated code.

// Gradient palette "ib_jul01_gp", originally from
// http://soliton.vm.bytemark.co.uk/pub/cpt-city/ing/xmas/tn/ib_jul01.png.index.html
// converted for FastLED with gammas (2.6, 2.2, 2.5)
// Size: 16 bytes of program space.

DEFINE_GRADIENT_PALETTE(ib_jul01_gp) {
	0, 194, 1, 1,
		94, 1, 29, 18,
		132, 57, 131, 28,
		255, 113, 1, 1
};

// Gradient palette "es_vintage_57_gp", originally from
// http://soliton.vm.bytemark.co.uk/pub/cpt-city/es/vintage/tn/es_vintage_57.png.index.html
// converted for FastLED with gammas (2.6, 2.2, 2.5)
// Size: 20 bytes of program space.

DEFINE_GRADIENT_PALETTE(es_vintage_57_gp) {
	0, 2, 1, 1,
		53, 18, 1, 0,
		104, 69, 29, 1,
		153, 167, 135, 10,
		255, 46, 56, 4
};

// Gradient palette "es_vintage_01_gp", originally from
// http://soliton.vm.bytemark.co.uk/pub/cpt-city/es/vintage/tn/es_vintage_01.png.index.html
// converted for FastLED with gammas (2.6, 2.2, 2.5)
// Size: 32 bytes of program space.

DEFINE_GRADIENT_PALETTE(es_vintage_01_gp) {
	0, 4, 1, 1,
		51, 16, 0, 1,
		76, 97, 104, 3,
		101, 255, 131, 19,
		127, 67, 9, 4,
		153, 16, 0, 1,
		229, 4, 1, 1,
		255, 4, 1, 1
};

// Gradient palette "es_rivendell_15_gp", originally from
// http://soliton.vm.bytemark.co.uk/pub/cpt-city/es/rivendell/tn/es_rivendell_15.png.index.html
// converted for FastLED with gammas (2.6, 2.2, 2.5)
// Size: 20 bytes of program space.

DEFINE_GRADIENT_PALETTE(es_rivendell_15_gp) {
	0, 1, 14, 5,
		101, 16, 36, 14,
		165, 56, 68, 30,
		242, 150, 156, 99,
		255, 150, 156, 99
};

// Gradient palette "rgi_15_gp", originally from
// http://soliton.vm.bytemark.co.uk/pub/cpt-city/ds/rgi/tn/rgi_15.png.index.html
// converted for FastLED with gammas (2.6, 2.2, 2.5)
// Size: 36 bytes of program space.

DEFINE_GRADIENT_PALETTE(rgi_15_gp) {
	0, 4, 1, 31,
		31, 55, 1, 16,
		63, 197, 3, 7,
		95, 59, 2, 17,
		127, 6, 2, 34,
		159, 39, 6, 33,
		191, 112, 13, 32,
		223, 56, 9, 35,
		255, 22, 6, 38
};

// Gradient palette "retro2_16_gp", originally from
// http://soliton.vm.bytemark.co.uk/pub/cpt-city/ma/retro2/tn/retro2_16.png.index.html
// converted for FastLED with gammas (2.6, 2.2, 2.5)
// Size: 8 bytes of program space.

DEFINE_GRADIENT_PALETTE(retro2_16_gp) {
	0, 188, 135, 1,
		255, 46, 7, 1
};

// Gradient palette "Analogous_1_gp", originally from
// http://soliton.vm.bytemark.co.uk/pub/cpt-city/nd/red/tn/Analogous_1.png.index.html
// converted for FastLED with gammas (2.6, 2.2, 2.5)
// Size: 20 bytes of program space.

DEFINE_GRADIENT_PALETTE(Analogous_1_gp) {
	0, 3, 0, 255,
		63, 23, 0, 255,
		127, 67, 0, 255,
		191, 142, 0, 45,
		255, 255, 0, 0
};

// Gradient palette "es_pinksplash_08_gp", originally from
// http://soliton.vm.bytemark.co.uk/pub/cpt-city/es/pink_splash/tn/es_pinksplash_08.png.index.html
// converted for FastLED with gammas (2.6, 2.2, 2.5)
// Size: 20 bytes of program space.

DEFINE_GRADIENT_PALETTE(es_pinksplash_08_gp) {
	0, 126, 11, 255,
		127, 197, 1, 22,
		175, 210, 157, 172,
		221, 157, 3, 112,
		255, 157, 3, 112
};

// Gradient palette "es_pinksplash_07_gp", originally from
// http://soliton.vm.bytemark.co.uk/pub/cpt-city/es/pink_splash/tn/es_pinksplash_07.png.index.html
// converted for FastLED with gammas (2.6, 2.2, 2.5)
// Size: 28 bytes of program space.

DEFINE_GRADIENT_PALETTE(es_pinksplash_07_gp) {
	0, 229, 1, 1,
		61, 242, 4, 63,
		101, 255, 12, 255,
		127, 249, 81, 252,
		153, 255, 11, 235,
		193, 244, 5, 68,
		255, 232, 1, 5
};

// Gradient palette "Coral_reef_gp", originally from
// http://soliton.vm.bytemark.co.uk/pub/cpt-city/nd/other/tn/Coral_reef.png.index.html
// converted for FastLED with gammas (2.6, 2.2, 2.5)
// Size: 24 bytes of program space.

DEFINE_GRADIENT_PALETTE(Coral_reef_gp) {
	0, 40, 199, 197,
		50, 10, 152, 155,
		96, 1, 111, 120,
		96, 43, 127, 162,
		139, 10, 73, 111,
		255, 1, 34, 71
};

// Gradient palette "es_ocean_breeze_068_gp", originally from
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
		183, 128, 57, 155,
		255, 146, 40, 123
};

// Gradient palette "Sunset_Real_gp", originally from
// http://soliton.vm.bytemark.co.uk/pub/cpt-city/nd/atmospheric/tn/Sunset_Real.png.index.html
// converted for FastLED with gammas (2.6, 2.2, 2.5)
// Size: 28 bytes of program space.

DEFINE_GRADIENT_PALETTE(Sunset_Real_gp) {
	0, 120, 0, 0,
		22, 179, 22, 0,
		51, 255, 104, 0,
		85, 167, 22, 18,
		135, 100, 0, 103,
		198, 16, 0, 130,
		255, 0, 0, 160
};

// Gradient palette "es_autumn_19_gp", originally from
// http://soliton.vm.bytemark.co.uk/pub/cpt-city/es/autumn/tn/es_autumn_19.png.index.html
// converted for FastLED with gammas (2.6, 2.2, 2.5)
// Size: 52 bytes of program space.

DEFINE_GRADIENT_PALETTE(es_autumn_19_gp) {
	0, 26, 1, 1,
		51, 67, 4, 1,
		84, 118, 14, 1,
		104, 137, 152, 52,
		112, 113, 65, 1,
		122, 133, 149, 59,
		124, 137, 152, 52,
		135, 113, 65, 1,
		142, 139, 154, 46,
		163, 113, 13, 1,
		204, 55, 3, 1,
		249, 17, 1, 1,
		255, 17, 1, 1
};

// Gradient palette "BlacK_Blue_Magenta_White_gp", originally from
// http://soliton.vm.bytemark.co.uk/pub/cpt-city/nd/basic/tn/BlacK_Blue_Magenta_White.png.index.html
// converted for FastLED with gammas (2.6, 2.2, 2.5)
// Size: 28 bytes of program space.

DEFINE_GRADIENT_PALETTE(BlacK_Blue_Magenta_White_gp) {
	0, 0, 0, 0,
		42, 0, 0, 45,
		84, 0, 0, 255,
		127, 42, 0, 255,
		170, 255, 0, 255,
		212, 255, 55, 255,
		255, 255, 255, 255
};

// Gradient palette "BlacK_Magenta_Red_gp", originally from
// http://soliton.vm.bytemark.co.uk/pub/cpt-city/nd/basic/tn/BlacK_Magenta_Red.png.index.html
// converted for FastLED with gammas (2.6, 2.2, 2.5)
// Size: 20 bytes of program space.

DEFINE_GRADIENT_PALETTE(BlacK_Magenta_Red_gp) {
	0, 0, 0, 0,
		63, 42, 0, 45,
		127, 255, 0, 255,
		191, 255, 0, 45,
		255, 255, 0, 0
};

// Gradient palette "BlacK_Red_Magenta_Yellow_gp", originally from
// http://soliton.vm.bytemark.co.uk/pub/cpt-city/nd/basic/tn/BlacK_Red_Magenta_Yellow.png.index.html
// converted for FastLED with gammas (2.6, 2.2, 2.5)
// Size: 28 bytes of program space.

DEFINE_GRADIENT_PALETTE(BlacK_Red_Magenta_Yellow_gp) {
	0, 0, 0, 0,
		42, 42, 0, 0,
		84, 255, 0, 0,
		127, 255, 0, 45,
		170, 255, 0, 255,
		212, 255, 55, 45,
		255, 255, 255, 0
};

// Gradient palette "Blue_Cyan_Yellow_gp", originally from
// http://soliton.vm.bytemark.co.uk/pub/cpt-city/nd/basic/tn/Blue_Cyan_Yellow.png.index.html
// converted for FastLED with gammas (2.6, 2.2, 2.5)
// Size: 20 bytes of program space.

DEFINE_GRADIENT_PALETTE(Blue_Cyan_Yellow_gp) {
	0, 0, 0, 255,
		63, 0, 55, 255,
		127, 0, 255, 255,
		191, 42, 255, 45,
		255, 255, 255, 0
};


// Single array of defined cpt-city color palettes.
// This will let us programmatically choose one based on
// a number, rather than having to activate each explicitly 
// by name every time.
// Since it is const, this array could also be moved 
// into PROGMEM to save SRAM, but for simplicity of illustration
// we'll keep it in a regular SRAM array.
//
// This list of color palettes acts as a "playlist"; you can
// add or delete, or re-arrange as you wish.
const TProgmemRGBGradientPalettePtr gGradientPalettes[] = {
  Sunset_Real_gp,
  es_rivendell_15_gp,
  es_ocean_breeze_036_gp,
  rgi_15_gp,
  retro2_16_gp,
  Analogous_1_gp,
  es_pinksplash_08_gp,
  Coral_reef_gp,
  es_ocean_breeze_068_gp,
  es_pinksplash_07_gp,
  es_vintage_01_gp,
  departure_gp,
  es_landscape_64_gp,
  es_landscape_33_gp,
  rainbowsherbet_gp,
  gr65_hult_gp,
  gr64_hult_gp,
  GMT_drywet_gp,
  ib_jul01_gp,
  es_vintage_57_gp,
  ib15_gp,
  Fuschia_7_gp,
  es_emerald_dragon_08_gp,
  lava_gp,
  fire_gp,
  Colorfull_gp,
  Magenta_Evening_gp,
  Pink_Purple_gp,
  es_autumn_19_gp,
  BlacK_Blue_Magenta_White_gp,
  BlacK_Magenta_Red_gp,
  BlacK_Red_Magenta_Yellow_gp,
  Blue_Cyan_Yellow_gp };


const uint8_t gGradientPaletteCount =
sizeof(gGradientPalettes) / sizeof(TProgmemRGBGradientPalettePtr) + 1; //one extra for rainbow palette

 const char* paletteNames[gGradientPaletteCount]  = {
  "Rainbow",
  "Sunset_Real",
  "Rivendell",
  "Ocean breeze 1",
  "RGI",
  "Retro",
  "Analogous_1",
  "Pink splash 1",
  "Coral reef",
  "Ocean breeze 2",
  "Pink splash 2",
  "Vintage 1",
  "Departure",
  "Landscape 1",
  "Landscape 2",
  "Rainbow sherbet",
  "GR65_hultp",
  "GR64_hult",
  "GMT_drywet",
  "July",
  "Vintage 2",
  "IB15",
  "Fuschia",
  "Emerald dragon",
  "Lava",
  "Fire",
  "Colorfull",
  "Magenta Evening",
  "Pink Purple",
  "Autumn",
  "Blue Magenta White",
  "Magenta Red",
  "Red Magenta Yellow",
  "Blue Cyan Yellow"
};

extern uint8_t Data::paletteIndex;
extern uint8_t Data::hbPaletteIndex;

VariableReference paletteIndex_t{ "Current Palette", &Data::paletteIndex, 0, 0, gGradientPaletteCount -1};
VariableReference paletteIndexHb_t{ "Current HB Palette", &Data::hbPaletteIndex, 0, 0, gGradientPaletteCount -1};



const char* getPaletteName(uint8_t i) {
	return paletteNames[i];
}
