jrhun/TeensyEngine/src/Patterns/PatternCube.h

#pragma once

#include "Pattern.h"
#include "../Cube.h"
#include <math.h>


class PatternCube : public _Pattern {
public:
	PatternCube() : _Pattern("Cube 3d") {
	}

	uint8_t drawFrame() {

		if (!_Pattern::useCustomEffect) {
			gfx.fade(128);
		}
		//gfx.blur(GuiVars1 * 127.0);

		engine.resetZ();

		auto it1 = cube.getTriangles<Vertex>(2.0f);
		auto it2 = cube.getTriangles<Vertex>(2.0f);

		Vec3 light1 = {
			float((cameraOffset + 3) * cos(angle + PI)),
			0.0f,
			float((cameraOffset + 3) * sin(angle + PI))
		};

		Mat3 m = Mat3::RotationX(angle)  * Mat3::RotationY(angle);
		for (auto &v : it1.vertices) {
			v.pos = v.pos * m;
			v.pos += light1;
		}

		Vec3 light2 = {
			float((-cameraOffset + 3) * cos(angle)),
			0.0f,
			float((-cameraOffset + 3) * sin(angle))
		};

		m = Mat3::RotationY(angle)  * Mat3::RotationX(angle);
		for (auto &v : it2.vertices) {
			
			v.pos = v.pos * m;
			v.pos += light2;
			//v.pos.x += (-cameraOffset + 3) * cos(angle);
			//v.pos.z += (-cameraOffset + 3) * sin(angle);
		}

		engine.pipeline.Draw(it1, light1);
		engine.pipeline.Draw(it2, light2);

		angle += 0.01;
		if (angle >= TWO_PI)
			angle -= TWO_PI;

		if (cameraOffset > 1)
			offsetDir = -1.0f;
		if (cameraOffset < -1)
			offsetDir = 1.0f;
		cameraOffset += 0.01 * offsetDir;

		return returnVal;
	}

	float cameraOffset = 0.0;
	float offsetDir = 1.0;
	float angle = 0;
	Cube cube;
	//VariableControl<float> v; 
};
